discount-cactus/LVDC-Remake/LVDC-Parts-Kicad/3dmodels/LDL1117S50R.step

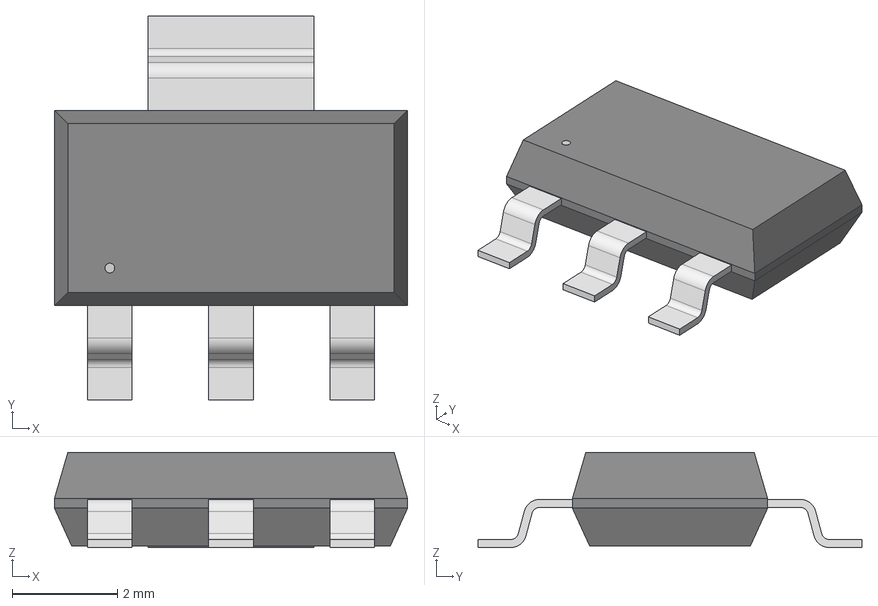
[picture p15: CAD file, 2024-02-13]
LVDC-Parts-Kicad/3dmodels/LDL1117S50R.step
6.71 x 7.29 x 1.81 mm
