discount-cactus/LVDC-Remake/LVDC-Parts-Kicad/3dmodels/TS50P07G.step

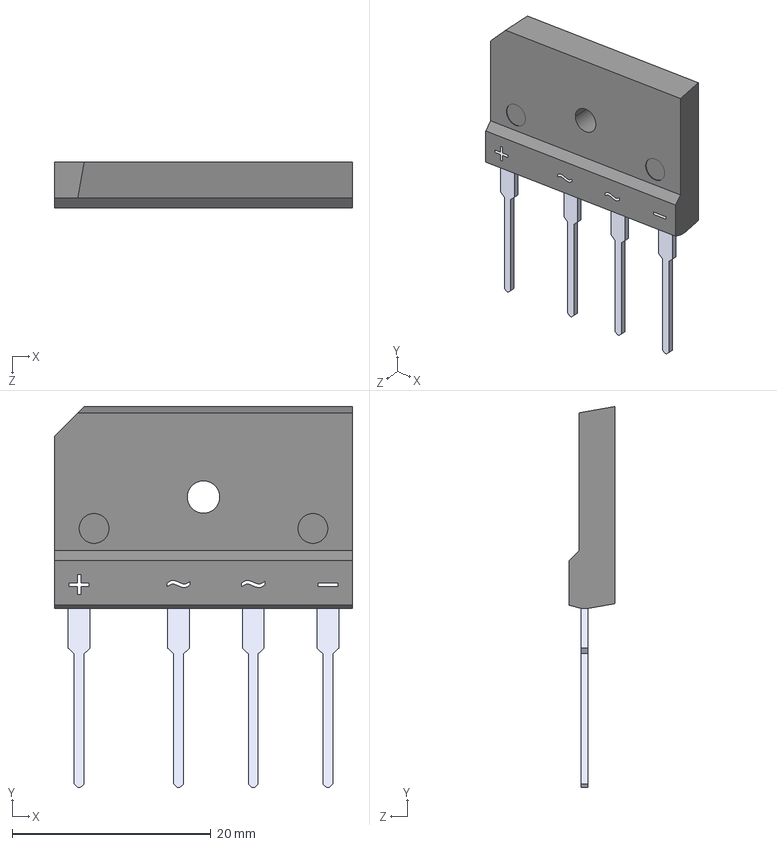
[picture p16: CAD file, 2024-02-13]
LVDC-Parts-Kicad/3dmodels/TS50P07G.step
30.0 x 38.3 x 4.60 mm
