discount-cactus/LVDC-Remake/LVDC-Parts-Kicad/3dmodels/DS3231M+TRL.step

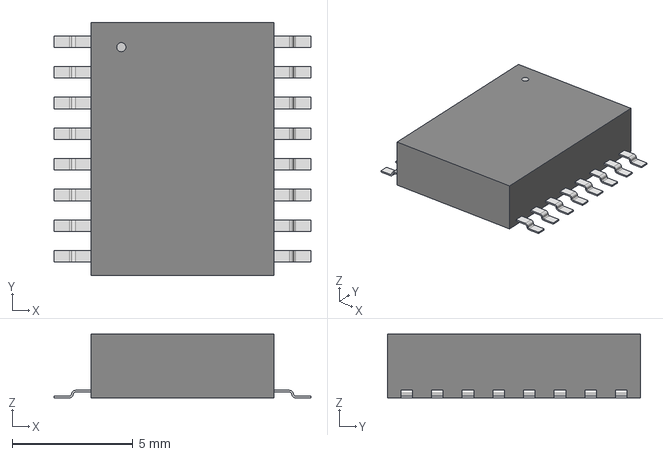
[picture p17: CAD file, 2024-02-13]
LVDC-Parts-Kicad/3dmodels/DS3231M+TRL.step
10.6 x 10.5 x 2.64 mm
