discount-cactus/LVDC-Remake/LVDC-Parts-Kicad/3dmodels/1043P.step

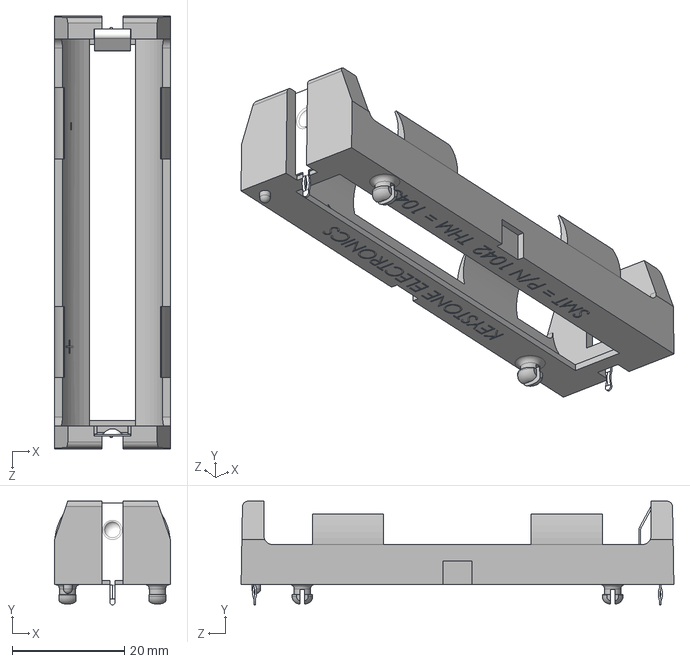
[picture p18: CAD file, 2024-02-13]
LVDC-Parts-Kicad/3dmodels/1043P.step
20.7 x 18.5 x 77.1 mm
