discount-cactus/LVDC-Remake/LVDC-Parts-Kicad/3dmodels/HEATSINK_658-45ABT4E.step

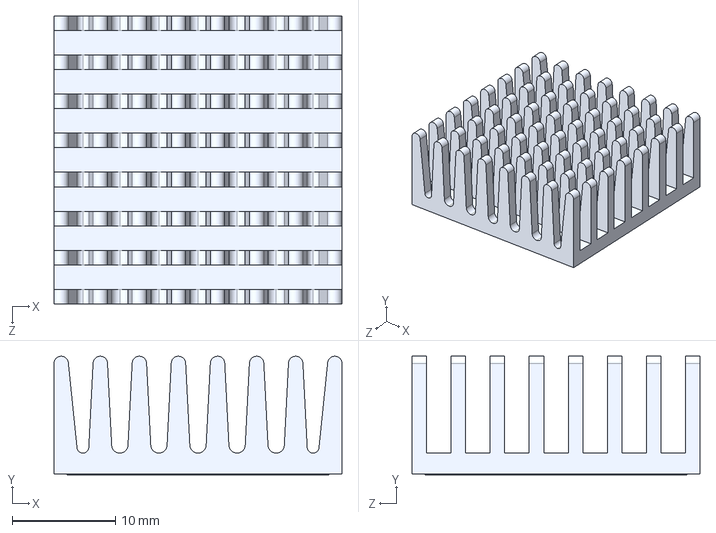
[picture p19: CAD file, 2024-02-13]
LVDC-Parts-Kicad/3dmodels/HEATSINK_658-45ABT4E.step
27.9 x 11.5 x 27.9 mm
