discount-cactus/LVDC-Remake/LVDC-Parts-Kicad/3dmodels/NYC0102BLT1G.step

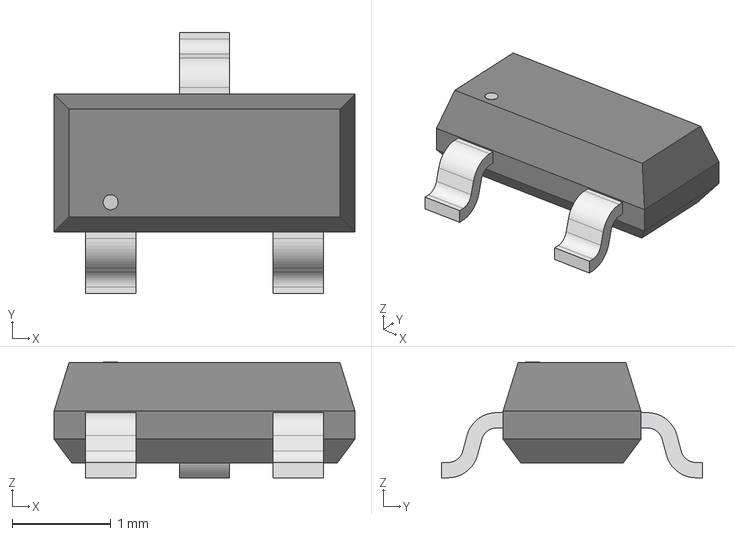
[picture p20: CAD file, 2024-02-13]
LVDC-Parts-Kicad/3dmodels/NYC0102BLT1G.step
3.05 x 2.64 x 1.17 mm
