discount-cactus/LVDC-Remake/LVDC-Parts-Kicad/3dmodels/6PCV_08_006.step

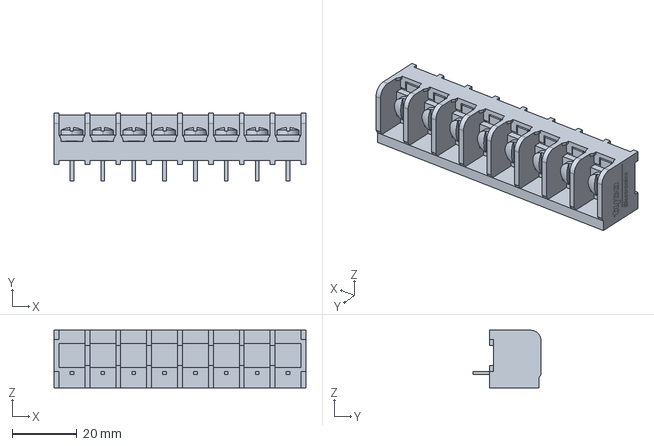
[picture p21: CAD file, 2024-02-13]
LVDC-Parts-Kicad/3dmodels/6PCV_08_006.step
77.7 x 21.0 x 17.8 mm
