discount-cactus/LVDC-Remake/LVDC-Parts-Kicad/3dmodels/TCLD1000.step

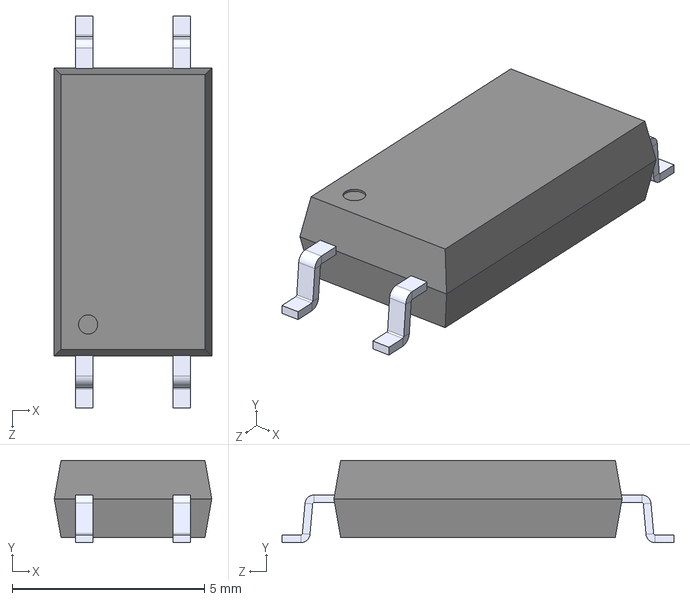
[picture p22: CAD file, 2024-02-13]
LVDC-Parts-Kicad/3dmodels/TCLD1000.step
4.10 x 2.14 x 10.2 mm
