discount-cactus/LVDC-Remake/LVDC-Parts-Kicad/3dmodels/PS2702-1-F3-A.step

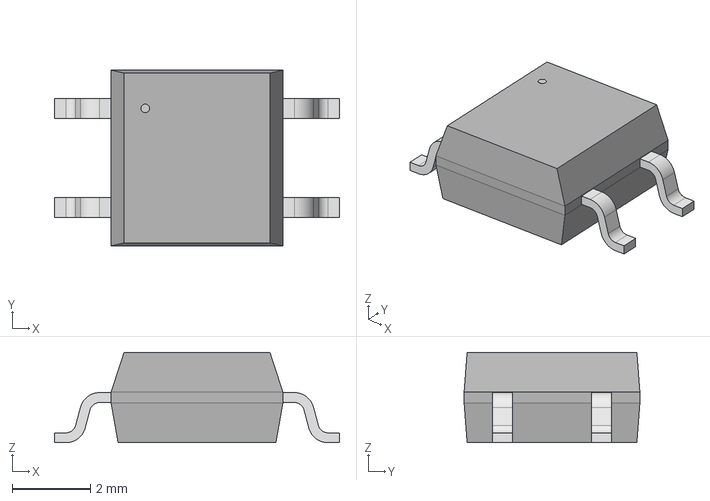
[picture p23: CAD file, 2024-02-13]
LVDC-Parts-Kicad/3dmodels/PS2702-1-F3-A.step
7.29 x 4.50 x 2.31 mm
