discount-cactus/LVDC-Remake/LVDC-Parts-Kicad/3dmodels/PDZVTR12B.step

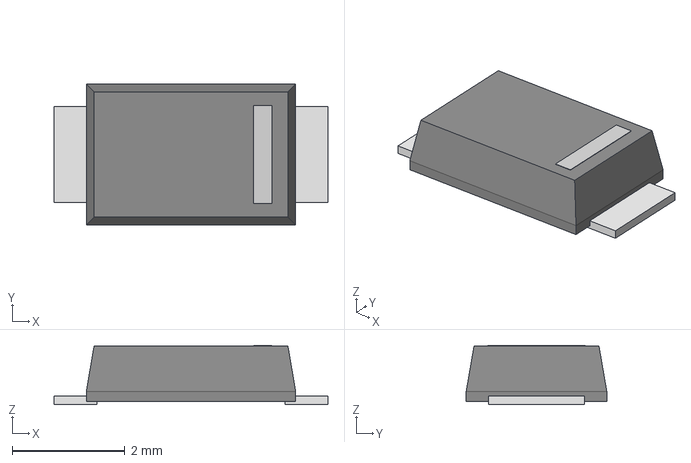
[picture p24: CAD file, 2024-02-13]
LVDC-Parts-Kicad/3dmodels/PDZVTR12B.step
4.85 x 2.49 x 1.05 mm
