discount-cactus/LVDC-Remake/LVDC-Parts-Kicad/3dmodels/SK510A_LTP.step

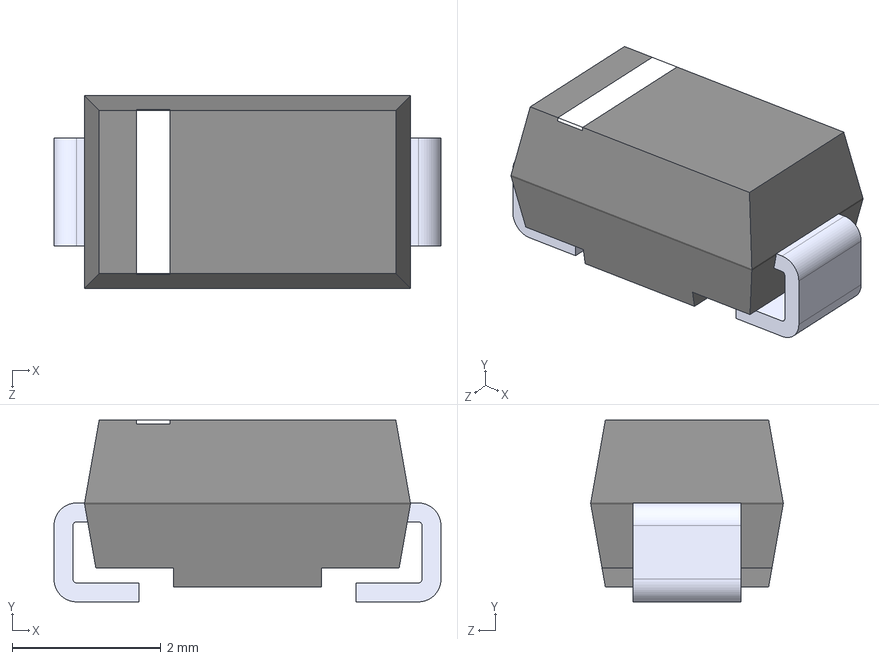
[picture p25: CAD file, 2024-02-13]
LVDC-Parts-Kicad/3dmodels/SK510A_LTP.step
5.20 x 2.44 x 2.58 mm
