discount-cactus/LVDC-Remake/LVDC-Parts-Kicad/3dmodels/MMSZ5240BT3G.step

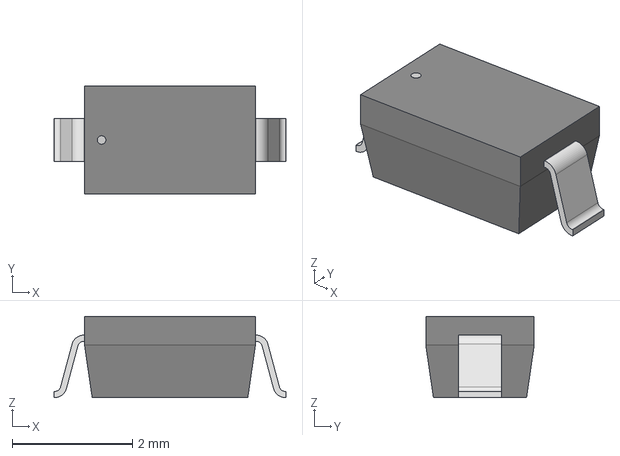
[picture p26: CAD file, 2024-02-13]
LVDC-Parts-Kicad/3dmodels/MMSZ5240BT3G.step
3.86 x 1.80 x 1.35 mm
