discount-cactus/LVDC-Remake/LVDC-Parts-Kicad/3dmodels/1101M2S3CQE2.step

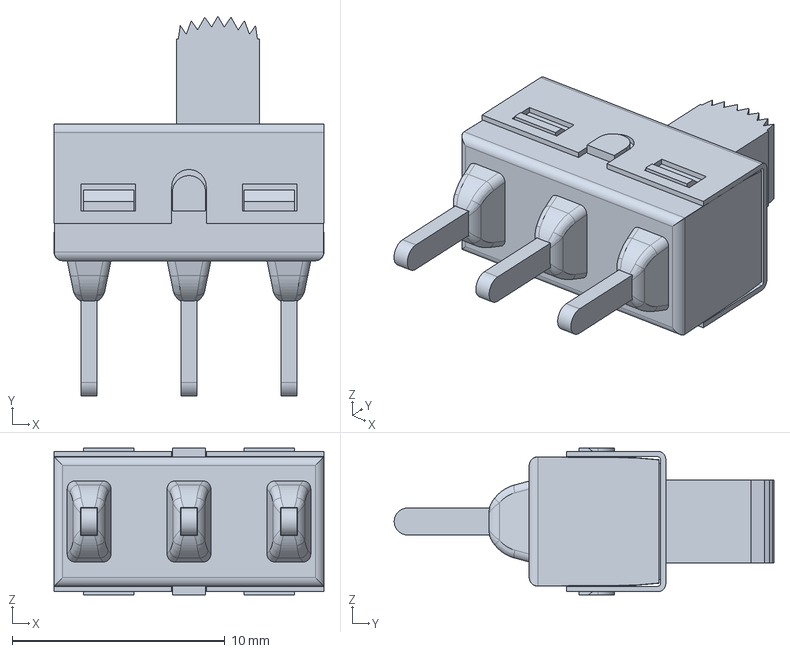
[picture p27: CAD file, 2024-02-13]
LVDC-Parts-Kicad/3dmodels/1101M2S3CQE2.step
12.7 x 17.9 x 6.91 mm
