discount-cactus/LVDC-Remake/LVDC-Parts-Kicad/3dmodels/HEATSINK_v2016b.step

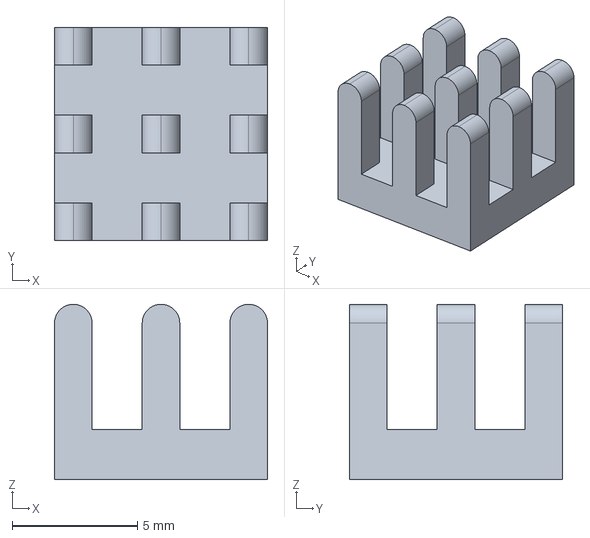
[picture p28: CAD file, 2024-02-13]
LVDC-Parts-Kicad/3dmodels/HEATSINK_v2016b.step
8.50 x 8.50 x 7.00 mm
