discount-cactus/LVDC-Remake/LVDC-Parts-Kicad/3dmodels/fan_30mm.step

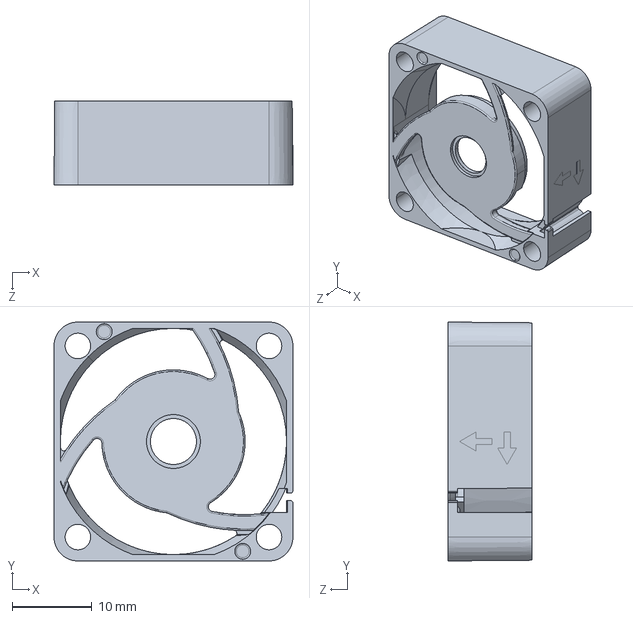
[picture p29: CAD file, 2024-02-13]
LVDC-Parts-Kicad/3dmodels/fan_30mm.step
30.0 x 30.0 x 10.5 mm
