discount-cactus/LVDC-Remake/LVDC-Parts-Kicad/3dmodels/1x6.step

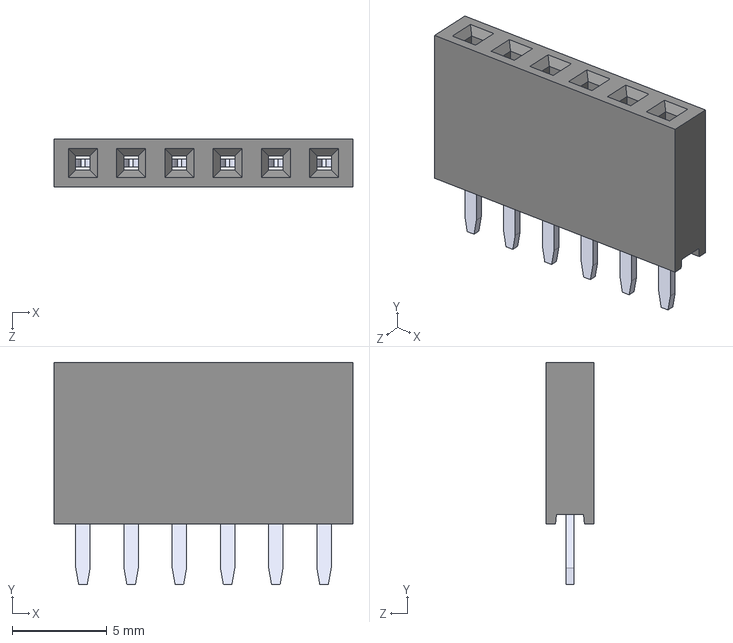
[picture p30: CAD file, 2024-02-13]
LVDC-Parts-Kicad/3dmodels/1x6.step
15.7 x 11.7 x 2.54 mm
