discount-cactus/LVDC-Remake/LVDC-Parts-Kicad/3dmodels/G5PZ-1A-E-DC5.step

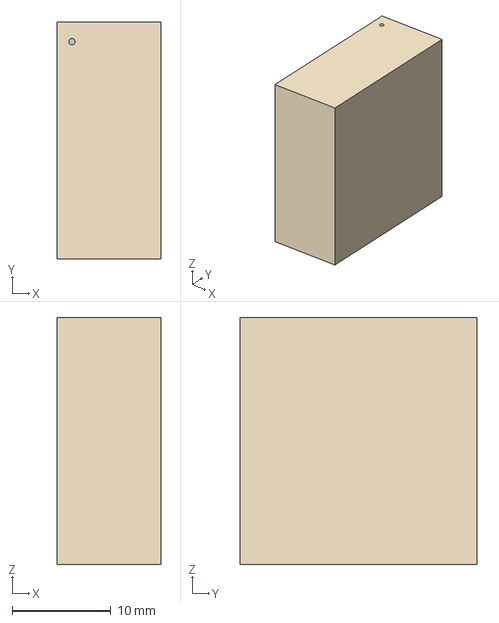
[picture p31: CAD file, 2024-02-13]
LVDC-Parts-Kicad/3dmodels/G5PZ-1A-E-DC5.step
10.5 x 24.0 x 25.0 mm
