discount-cactus/LVDC-Remake/LVDC-Parts-Kicad/3dmodels/SIC431AED-T1-GE3.step

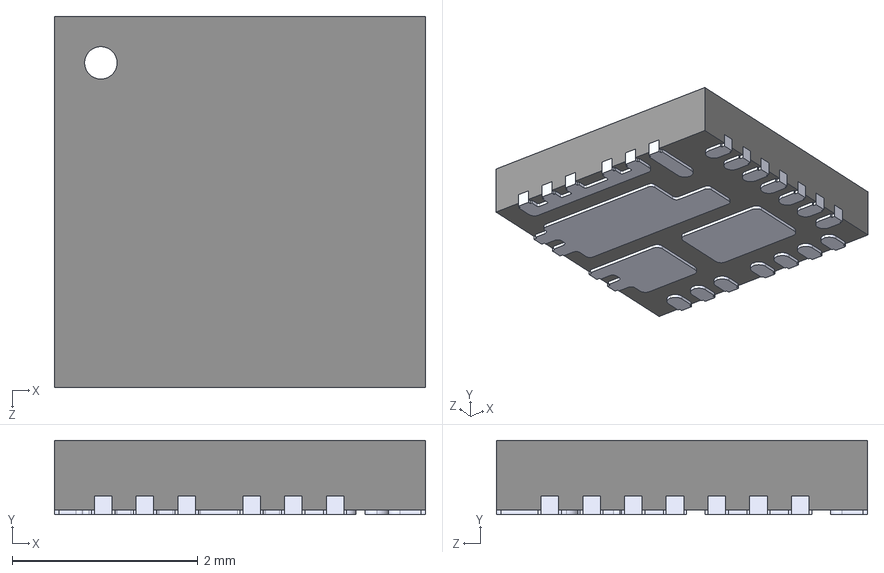
[picture p32: CAD file, 2024-02-13]
LVDC-Parts-Kicad/3dmodels/SIC431AED-T1-GE3.step
4.00 x 0.8 x 4.00 mm
