discount-cactus/LVDC-Remake/LVDC-Parts-Kicad/3dmodels/SBR10U200P5-13.step

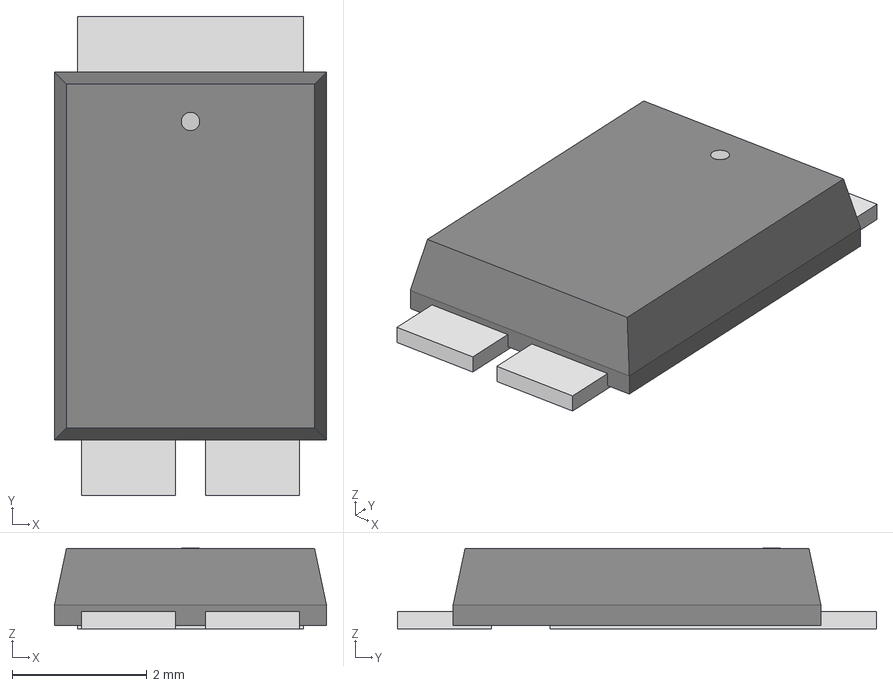
[picture p33: CAD file, 2024-02-13]
LVDC-Parts-Kicad/3dmodels/SBR10U200P5-13.step
4.04 x 7.11 x 1.20 mm
