discount-cactus/LVDC-Remake/LVDC-Parts-Kicad/3dmodels/MEM2051-00-195-00-A.step

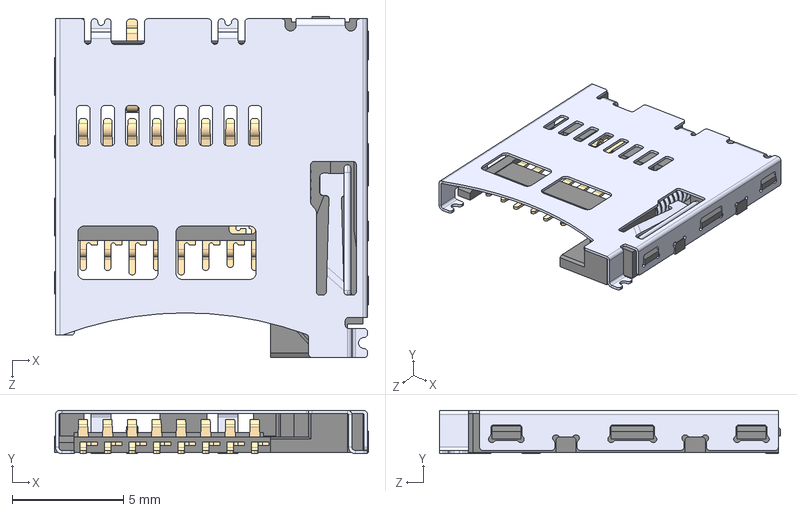
[picture p34: CAD file, 2024-02-13]
LVDC-Parts-Kicad/3dmodels/MEM2051-00-195-00-A.step
14.1 x 1.95 x 15.3 mm
