discount-cactus/LVDC-Remake/LVDC-Parts-Kicad/3dmodels/8PCV_02_006.step

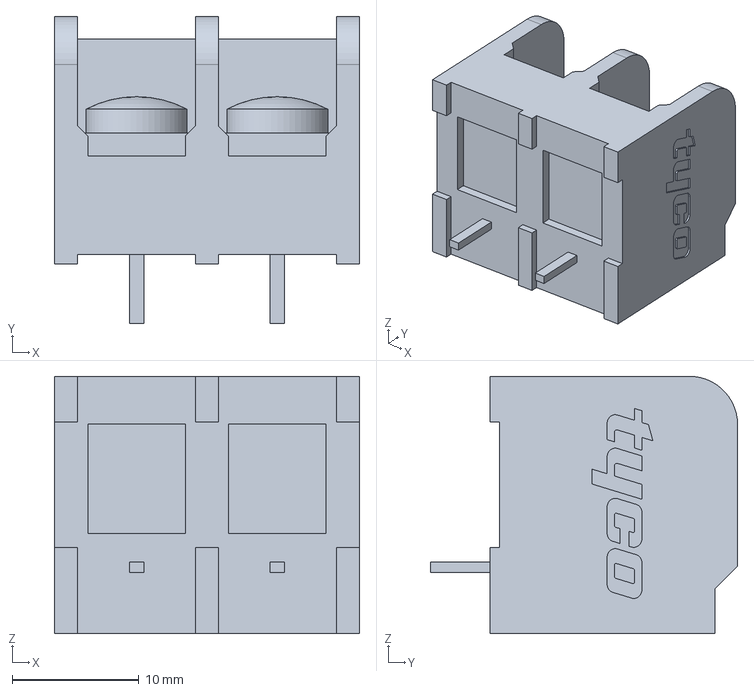
[picture p35: CAD file, 2024-02-13]
LVDC-Parts-Kicad/3dmodels/8PCV_02_006.step
24.1 x 24.3 x 20.3 mm
