discount-cactus/LVDC-Remake/LVDC-Parts-Kicad/3dmodels/G2RL_1A_E2_CV_HA.step

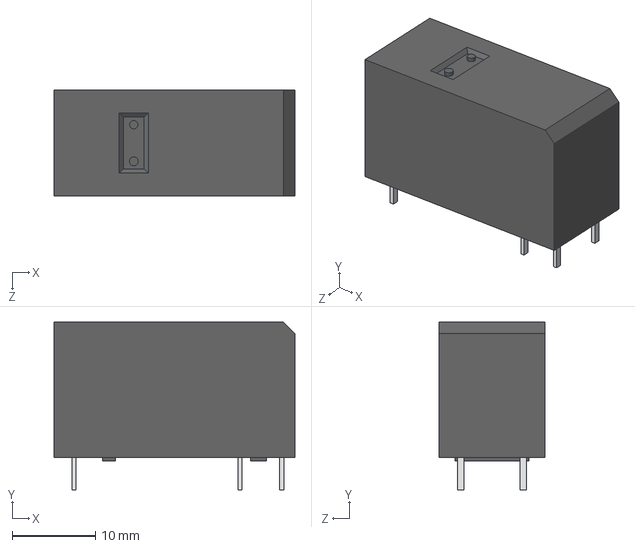
[picture p36: CAD file, 2024-02-13]
LVDC-Parts-Kicad/3dmodels/G2RL_1A_E2_CV_HA.step
29.0 x 20.2 x 12.7 mm
