discount-cactus/LVDC-Remake/LVDC-Parts-Kicad/3dmodels/Fuse_15A.step

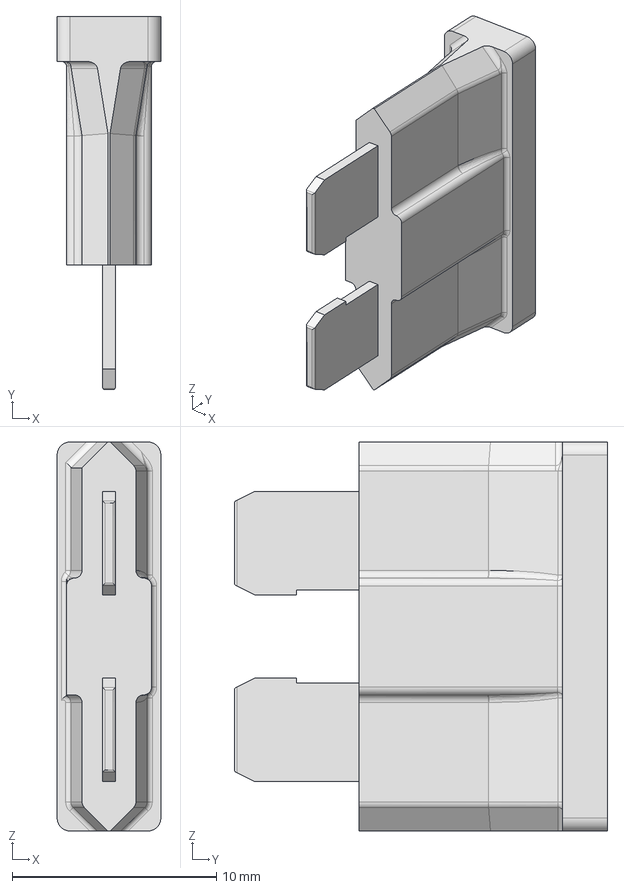
[picture p37: CAD file, 2023-09-17]
LVDC-Parts-Kicad/3dmodels/Fuse_15A.step
5.08 x 18.3 x 19.0 mm
