discount-cactus/LVDC-Remake/LVDC-Parts-Kicad/3dmodels/1x14.step

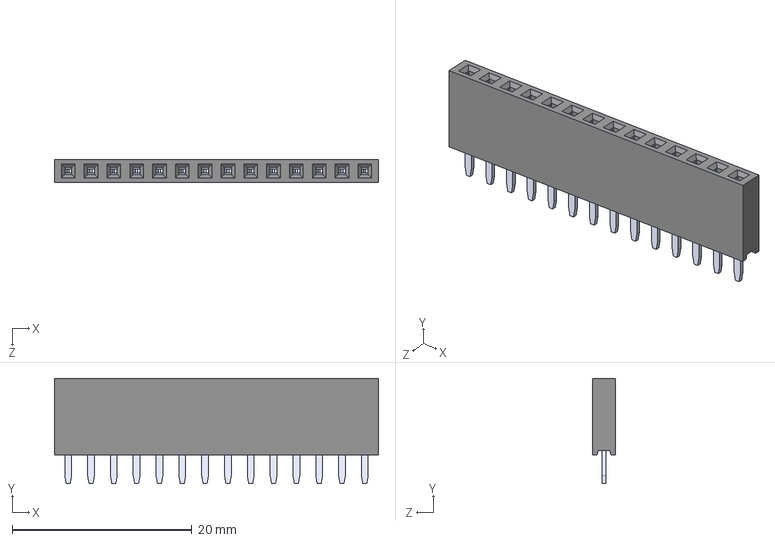
[picture p38: CAD file, 2023-08-25]
LVDC-Parts-Kicad/3dmodels/1x14.step
36.1 x 11.7 x 2.54 mm
