discount-cactus/LVDC-Remake/LVDC-Parts-Kicad/3dmodels/L7805CV.step

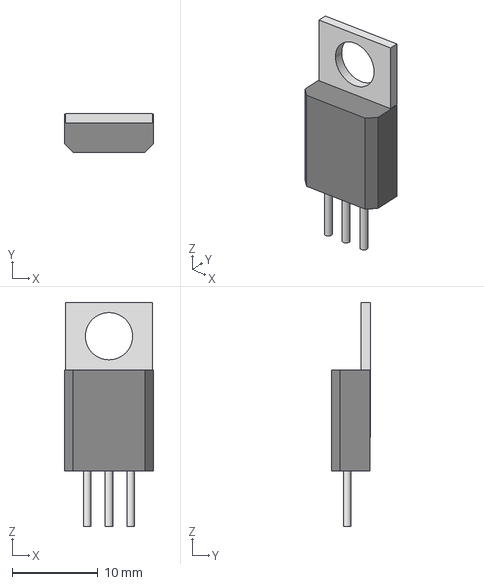
[picture p39: CAD file, 2023-08-25]
LVDC-Parts-Kicad/3dmodels/L7805CV.step
10.4 x 4.60 x 26.2 mm
