discount-cactus/LVDC-Remake/LVDC-Parts-Kicad/3dmodels/SN74HCS30PWR.STEP

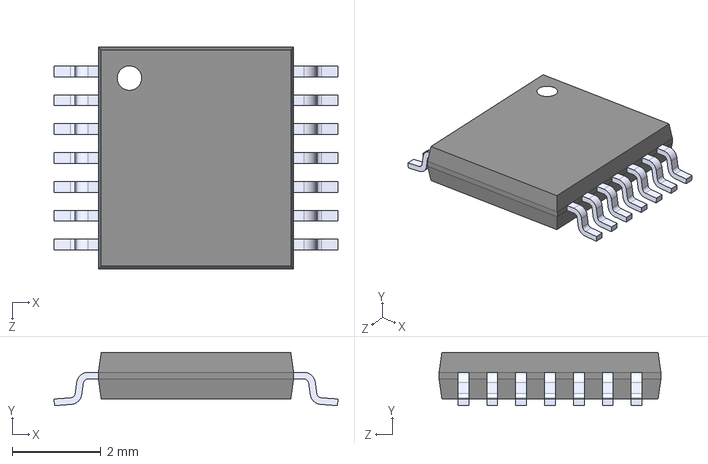
[picture p40: CAD file, 2023-08-25]
LVDC-Parts-Kicad/3dmodels/SN74HCS30PWR.STEP
6.40 x 1.20 x 5.00 mm
