discount-cactus/LVDC-Remake/LVDC-Parts-Kicad/3dmodels/1x10.step

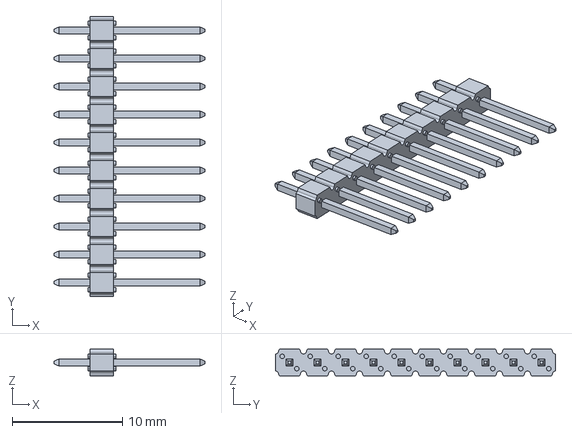
[picture p41: CAD file, 2023-08-25]
LVDC-Parts-Kicad/3dmodels/1x10.step
13.7 x 25.4 x 2.41 mm
