discount-cactus/LVDC-Remake/LVDC-Parts-Kicad/3dmodels/A767KN476M1HLAE029.step

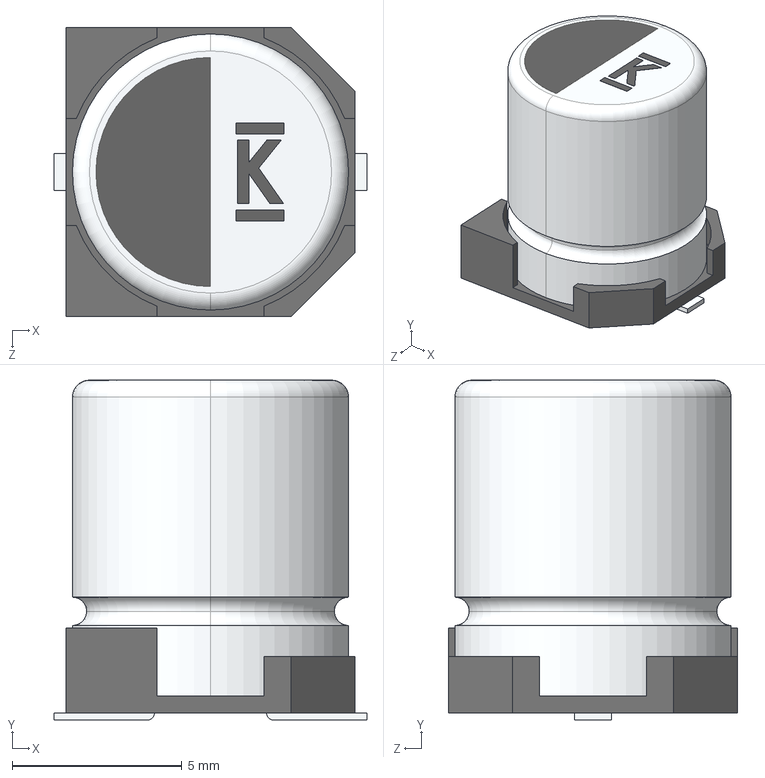
[picture p42: CAD file, 2023-08-25]
LVDC-Parts-Kicad/3dmodels/A767KN476M1HLAE029.step
9.20 x 10.0 x 8.50 mm
