discount-cactus/LVDC-Remake/LVDC-Parts-Kicad/3dmodels/2x19.step

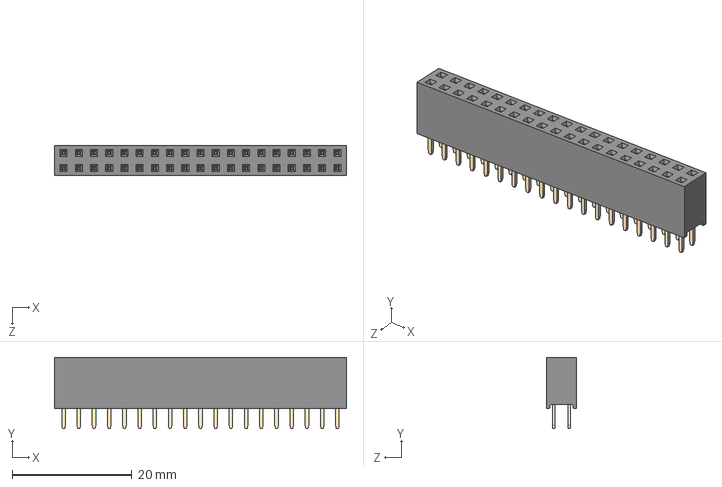
[picture p43: CAD file, 2023-08-25]
LVDC-Parts-Kicad/3dmodels/2x19.step
48.8 x 11.9 x 5.08 mm
2 row tin body_19
2 row tin pins x 19
