discount-cactus/LVDC-Remake/LVDC-Parts-Kicad/3dmodels/2x13.step

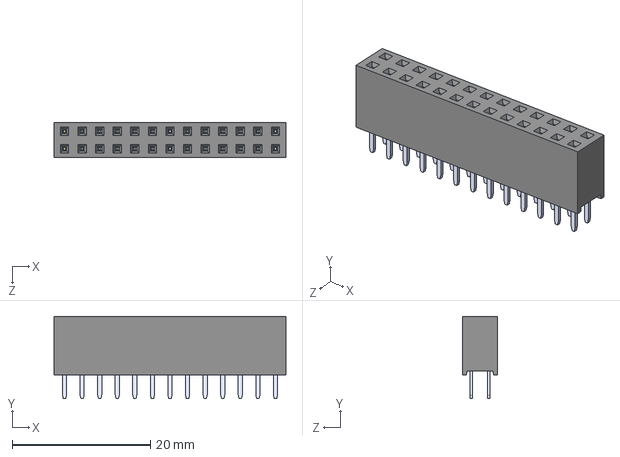
[picture p44: CAD file, 2023-08-25]
LVDC-Parts-Kicad/3dmodels/2x13.step
33.5 x 11.9 x 5.08 mm
2 row tin body_13
2 row tin pins x 13
