discount-cactus/LVDC-Remake/LVDC-Parts-Kicad/3dmodels/LM350T.step

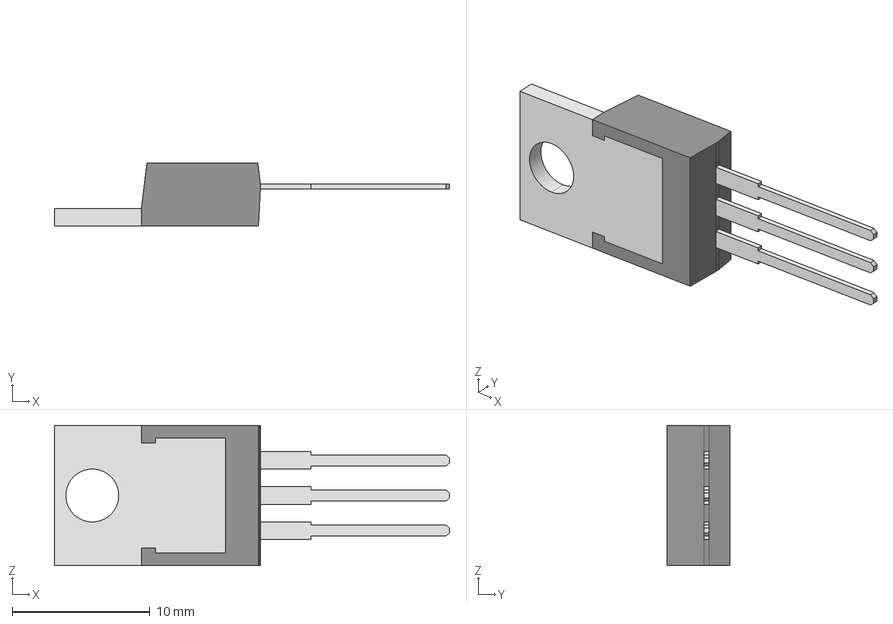
[picture p45: CAD file, 2023-08-25]
LVDC-Parts-Kicad/3dmodels/LM350T.step
28.7 x 4.57 x 10.2 mm
T03B_BODY
T03B_LEAD x 3
T03B_HS
