discount-cactus/LVDC-Remake/LVDC-Parts-Kicad/3dmodels/1N4736A.step

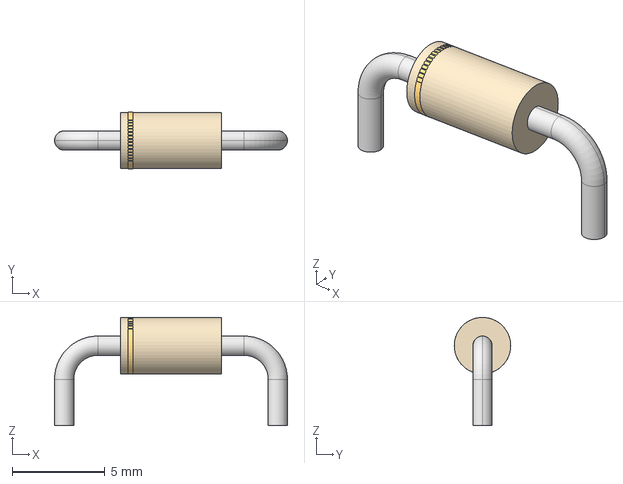
[picture p46: CAD file, 2023-08-25]
LVDC-Parts-Kicad/3dmodels/1N4736A.step
12.6 x 3.05 x 5.84 mm
