discount-cactus/LVDC-Remake/LVDC-Parts-Kicad/3dmodels/SRR1208-6R5ML.step

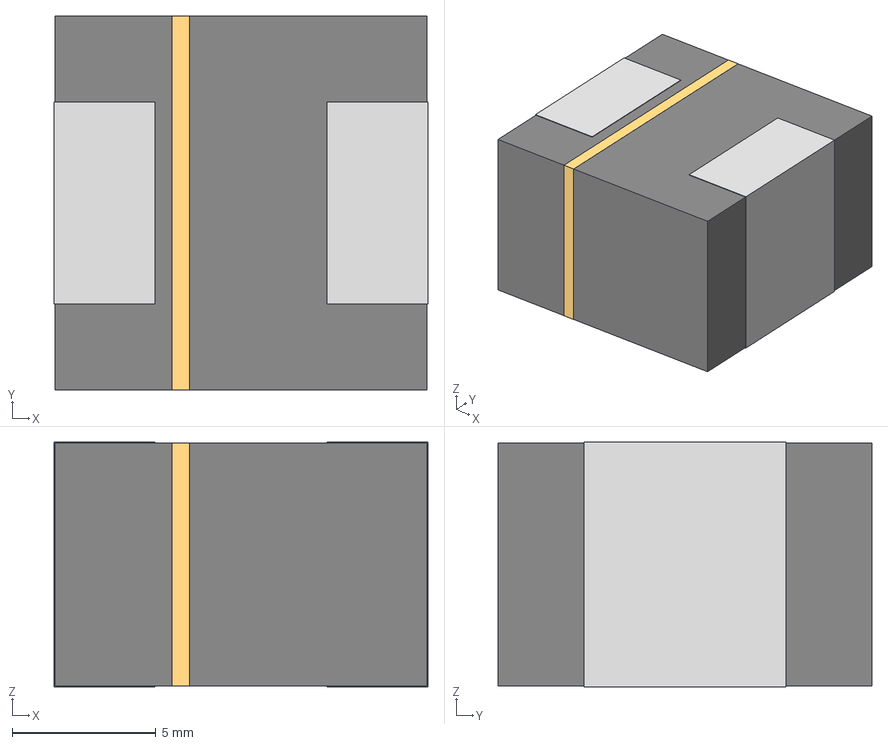
[picture p47: CAD file, 2023-08-25]
LVDC-Parts-Kicad/3dmodels/SRR1208-6R5ML.step
13.0 x 13.0 x 8.51 mm
