discount-cactus/LVDC-Remake/LVDC-Parts-Kicad/3dmodels/C_PTH_680uF.step

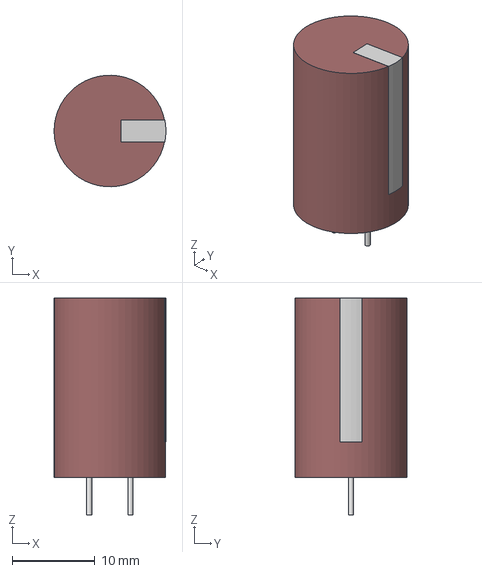
[picture p48: CAD file, 2023-08-25]
LVDC-Parts-Kicad/3dmodels/C_PTH_680uF.step
13.5 x 13.5 x 26.3 mm
