discount-cactus/LVDC-Remake/LVDC-Parts-Kicad/3dmodels/2x18.step

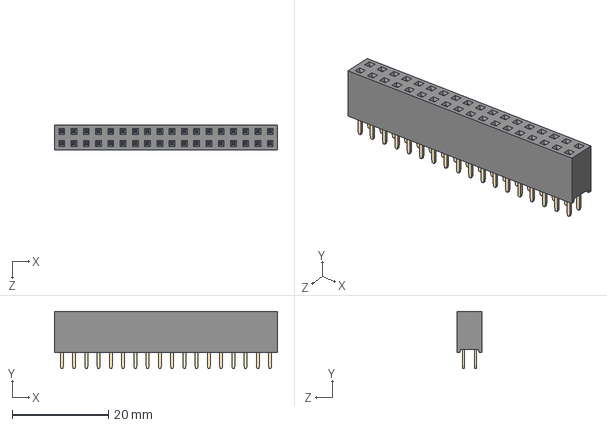
[picture p49: CAD file, 2023-08-25]
LVDC-Parts-Kicad/3dmodels/2x18.step
46.2 x 11.9 x 5.08 mm
2 row tin body_18
2 row tin pins x 18
