discount-cactus/LVDC-Remake/LVDC-Parts-Kicad/3dmodels/AMC1301QDWVQ1.step

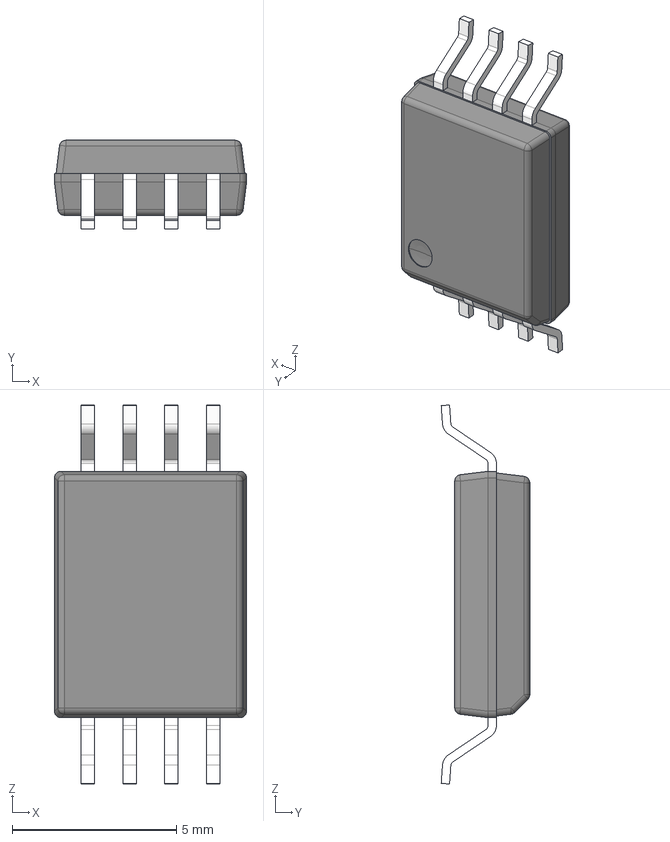
[picture p50: CAD file, 2023-08-25]
LVDC-Parts-Kicad/3dmodels/AMC1301QDWVQ1.step
5.85 x 2.70 x 11.5 mm
BODY-SOIC
LEAD-DWV0008A x 8
