discount-cactus/LVDC-Remake/LVDC-Parts-Kicad/3dmodels/2x12.step

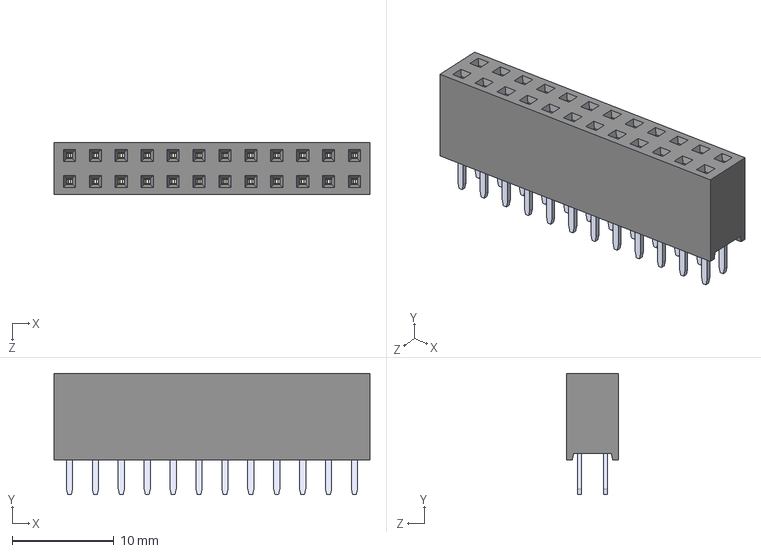
[picture p51: CAD file, 2023-08-25]
LVDC-Parts-Kicad/3dmodels/2x12.step
31.0 x 11.9 x 5.08 mm
2 row tin body_12
2 row tin pins x 12
