discount-cactus/LVDC-Remake/LVDC-Parts-Kicad/3dmodels/SOD_128.step

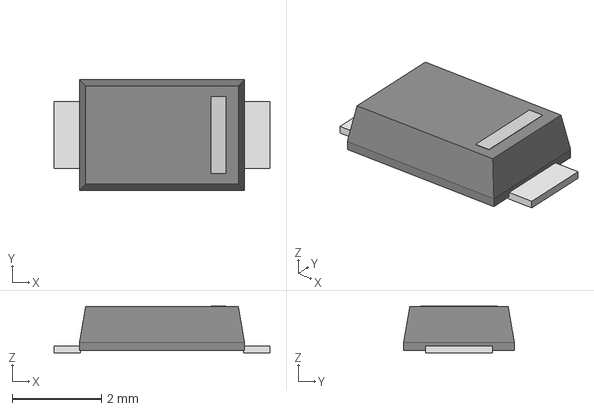
[picture p52: CAD file, 2023-08-25]
LVDC-Parts-Kicad/3dmodels/SOD_128.step
4.85 x 2.49 x 1.05 mm
