discount-cactus/LVDC-Remake/LVDC-Parts-Kicad/3dmodels/2x2.step

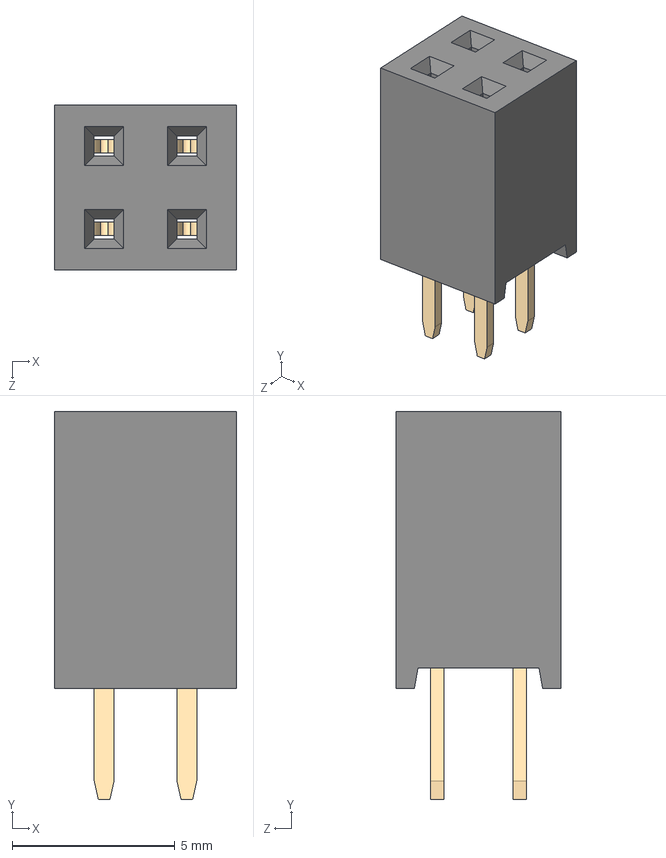
[picture p53: CAD file, 2023-08-25]
LVDC-Parts-Kicad/3dmodels/2x2.step
5.59 x 11.9 x 5.08 mm
2 row tin body_02
2 row tin pins x 2
