discount-cactus/LVDC-Remake/LVDC-Parts-Kicad/3dmodels/INA210AIDCKR.step

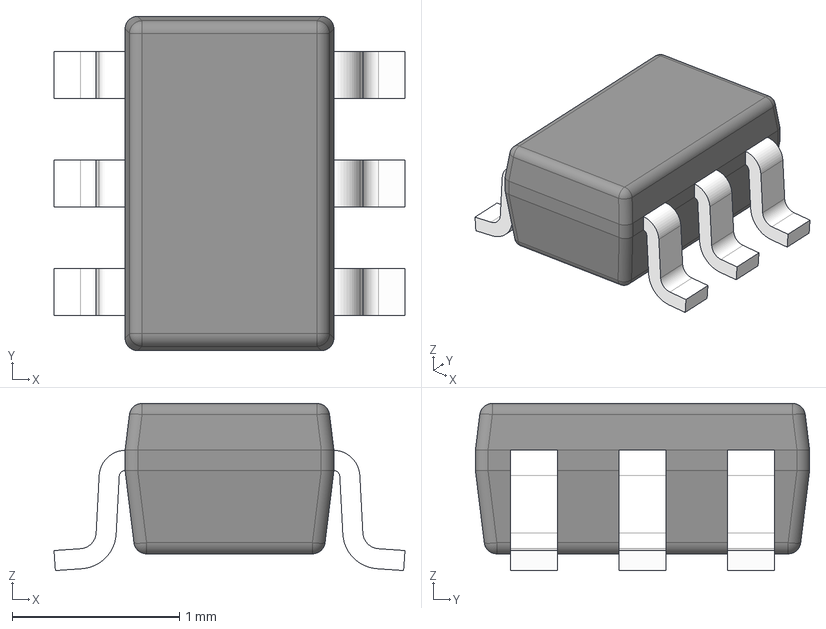
[picture p54: CAD file, 2023-08-25]
LVDC-Parts-Kicad/3dmodels/INA210AIDCKR.step
2.10 x 2.00 x 1.00 mm
BODY-SOT
LEAD-SOT x 6
PIN1-ID
