discount-cactus/LVDC-Remake/LVDC-Parts-Kicad/3dmodels/A750MV477M1VAAE018.step

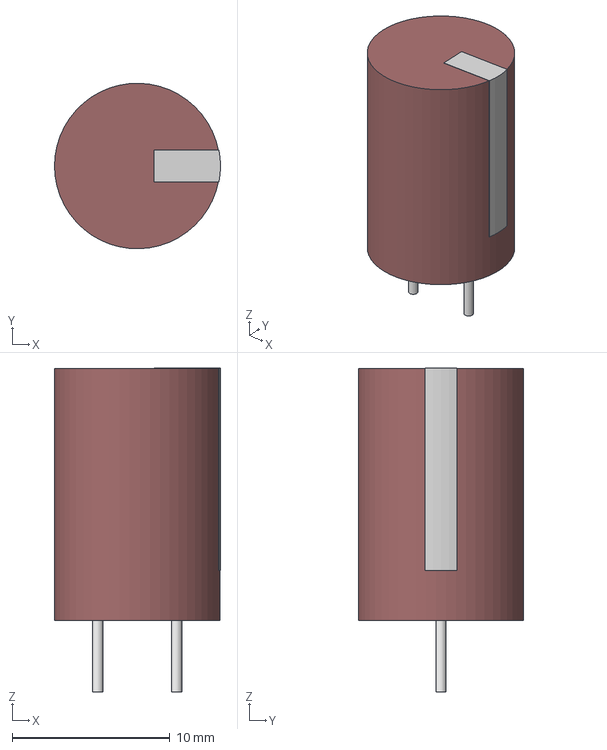
[picture p55: CAD file, 2023-08-25]
LVDC-Parts-Kicad/3dmodels/A750MV477M1VAAE018.step
10.5 x 10.5 x 20.5 mm
