discount-cactus/LVDC-Remake/LVDC-Parts-Kicad/3dmodels/DO-214BA.step

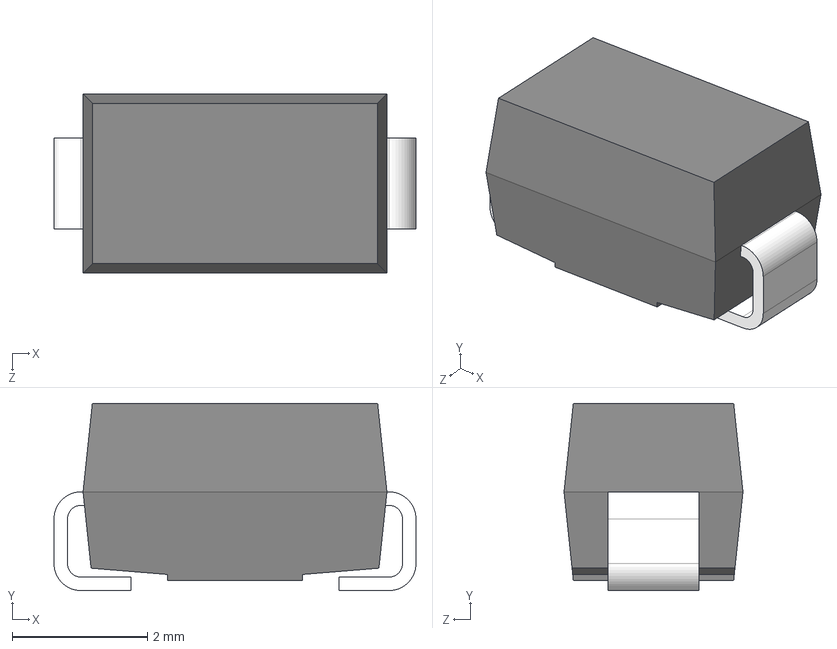
[picture p56: CAD file, 2023-08-25]
LVDC-Parts-Kicad/3dmodels/DO-214BA.step
5.36 x 2.77 x 2.65 mm
