discount-cactus/LVDC-Remake/LVDC-Parts-Kicad/3dmodels/2x23.step

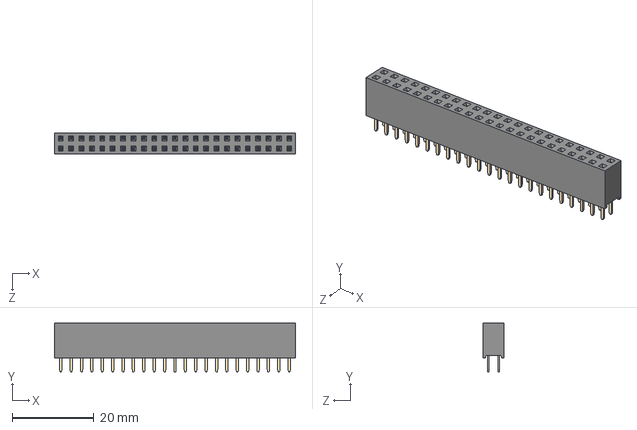
[picture p57: CAD file, 2023-08-25]
LVDC-Parts-Kicad/3dmodels/2x23.step
58.9 x 11.9 x 5.08 mm
2 row tin body_23
2 row tin pins x 23
