discount-cactus/LVDC-Remake/LVDC-Parts-Kicad/3dmodels/ETQ-P6F4R1LFA.step

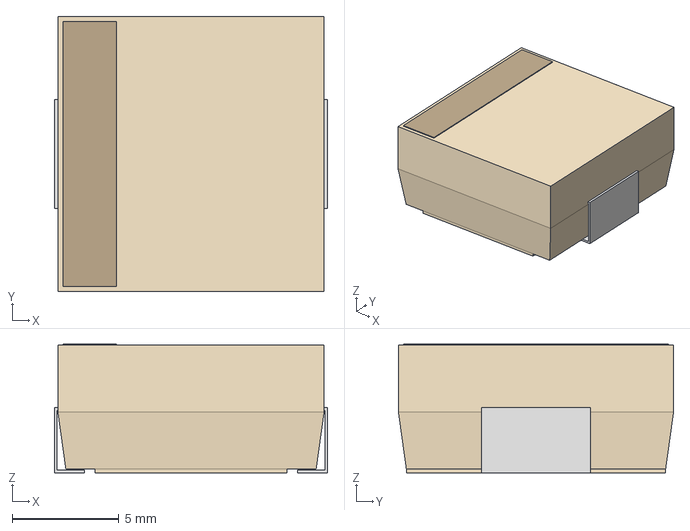
[picture p58: CAD file, 2023-08-25]
LVDC-Parts-Kicad/3dmodels/ETQ-P6F4R1LFA.step
12.8 x 12.9 x 6.04 mm
