discount-cactus/LVDC-Remake/LVDC-Parts-Kicad/3dmodels/CAP_PTH.step

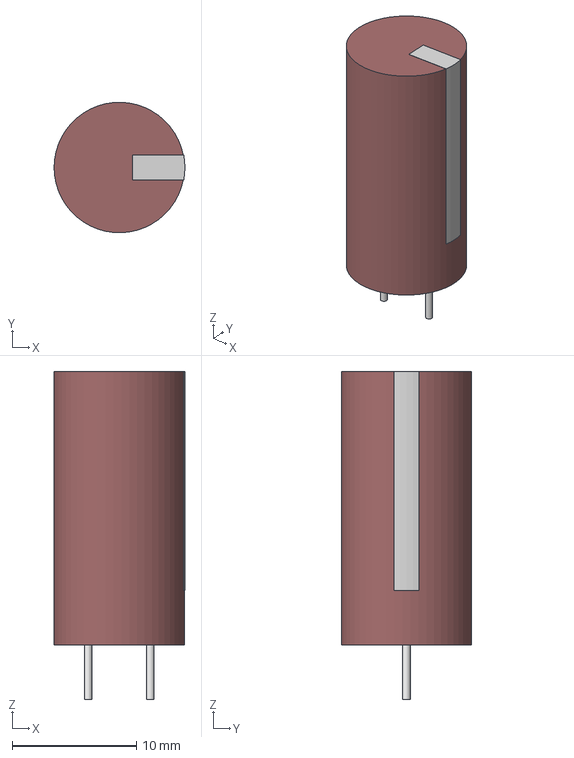
[picture p59: CAD file, 2023-05-30]
LVDC-Parts-Kicad/3dmodels/CAP_PTH.step
10.5 x 10.5 x 26.4 mm
