discount-cactus/LVDC-Remake/LVDC-Parts-Kicad/3dmodels/W5500.step

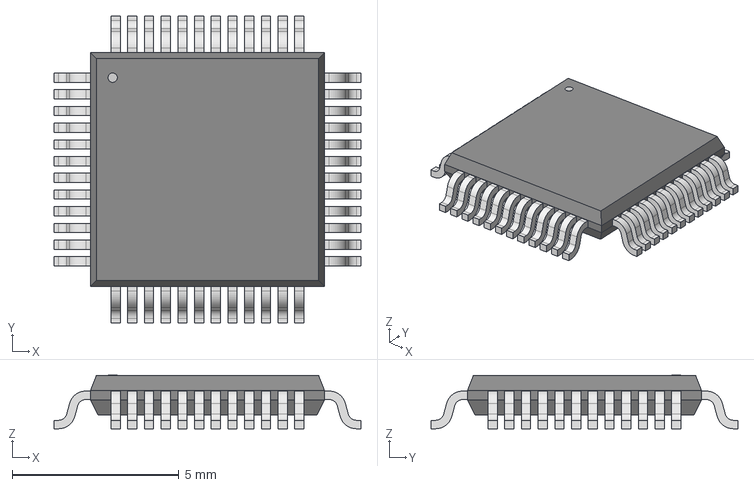
[picture p60: CAD file, 2023-05-30]
LVDC-Parts-Kicad/3dmodels/W5500.step
9.19 x 9.19 x 1.60 mm
