discount-cactus/LVDC-Remake/LVDC-Parts-Kicad/3dmodels/2x30.STEP

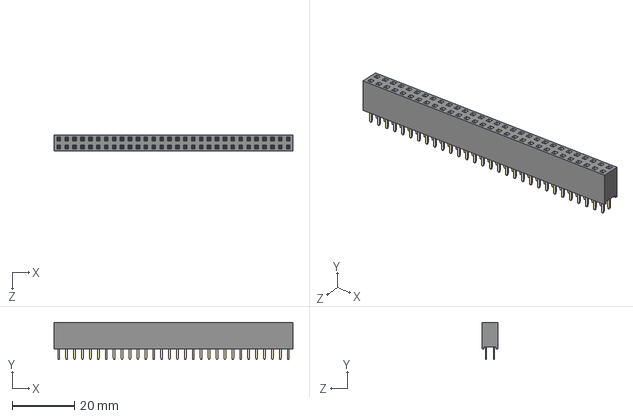
[picture p61: CAD file, 2023-05-30]
LVDC-Parts-Kicad/3dmodels/2x30.STEP
76.7 x 11.9 x 5.08 mm
2 row tin body_30
2 row tin pins x 30
