discount-cactus/LVDC-Remake/LVDC-Parts-Kicad/3dmodels/PPTC102LJBN-RC.step

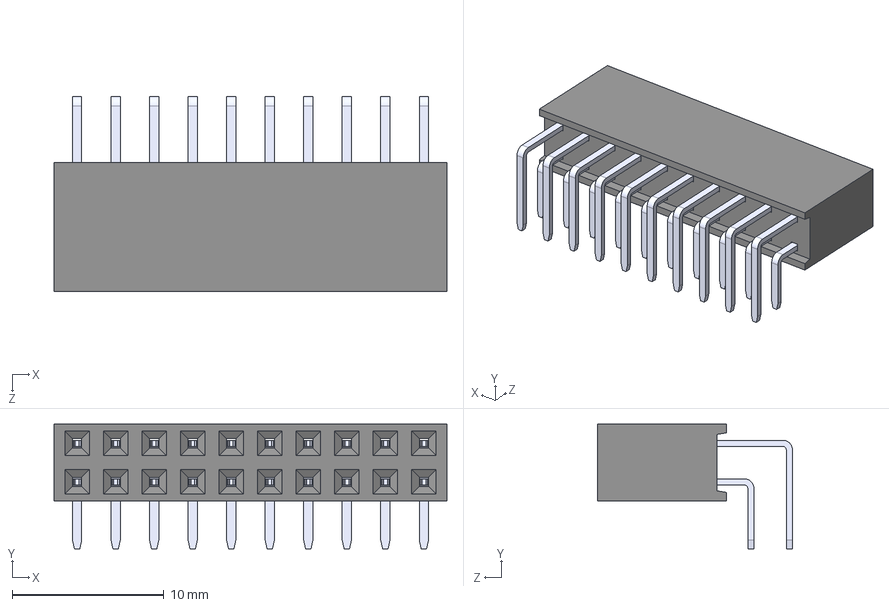
[picture p62: CAD file, 2023-05-30]
LVDC-Parts-Kicad/3dmodels/PPTC102LJBN-RC.step
25.9 x 8.23 x 12.9 mm
