discount-cactus/LVDC-Remake/LVDC-Parts-Kicad/3dmodels/FB_0805.step

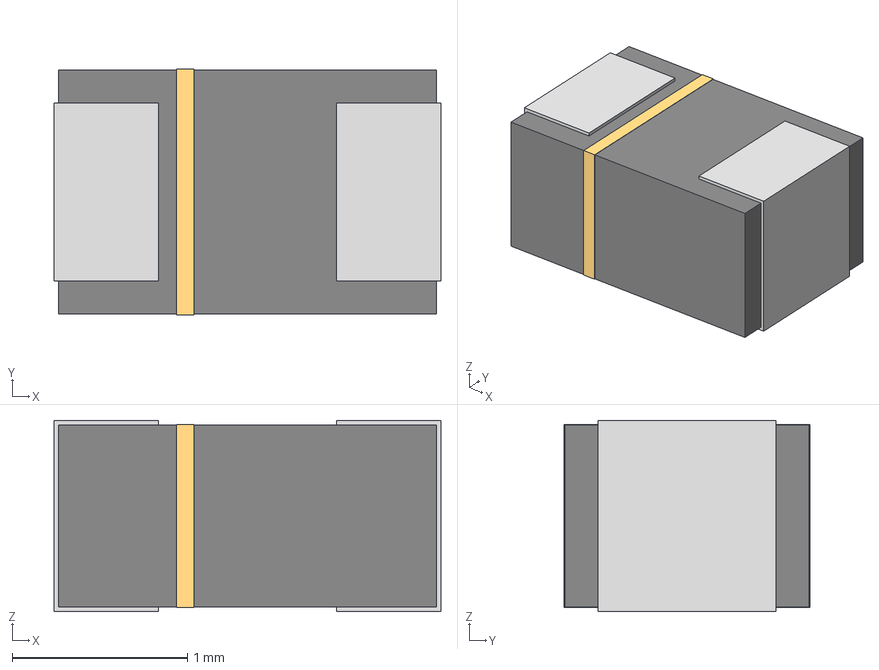
[picture p63: CAD file, 2023-05-30]
LVDC-Parts-Kicad/3dmodels/FB_0805.step
2.21 x 1.40 x 1.09 mm
