discount-cactus/LVDC-Remake/LVDC-Parts-Kicad/3dmodels/1x3.step

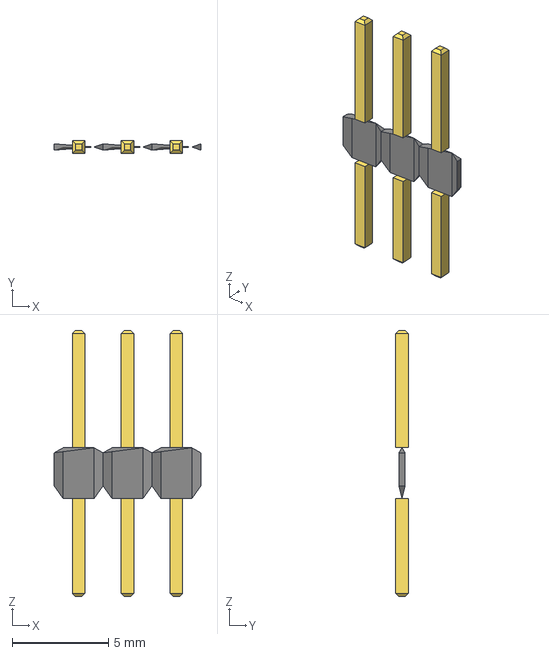
[picture p64: CAD file, 2023-05-30]
LVDC-Parts-Kicad/3dmodels/1x3.step
7.62 x 0.66 x 13.8 mm
