discount-cactus/LVDC-Remake/LVDC-Parts-Kicad/3dmodels/CD4002BNSR.step

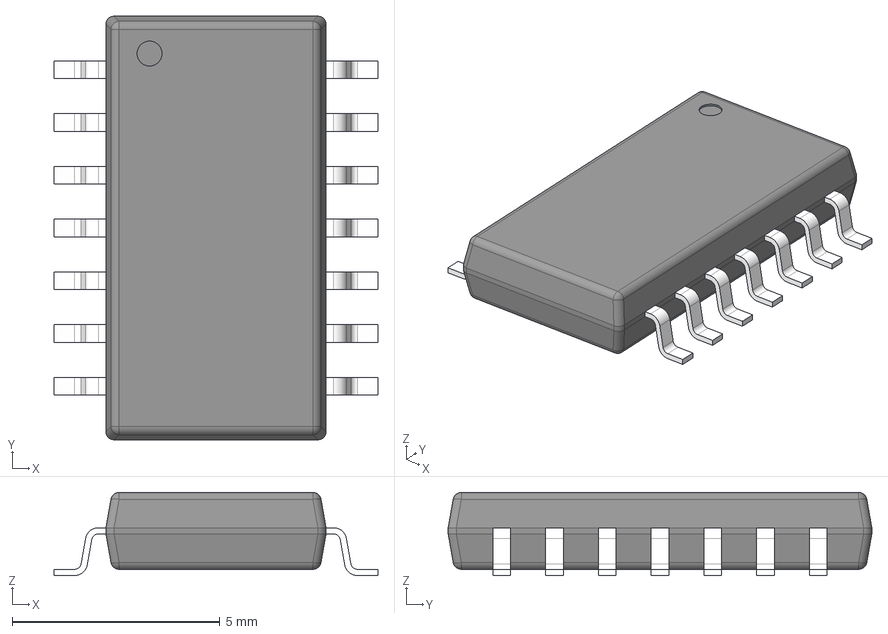
[picture p65: CAD file, 2023-05-30]
LVDC-Parts-Kicad/3dmodels/CD4002BNSR.step
7.80 x 10.2 x 2.00 mm
BODY-SO
LEAD-SO x 14
