discount-cactus/LVDC-Remake/LVDC-Parts-Kicad/3dmodels/2x5.step

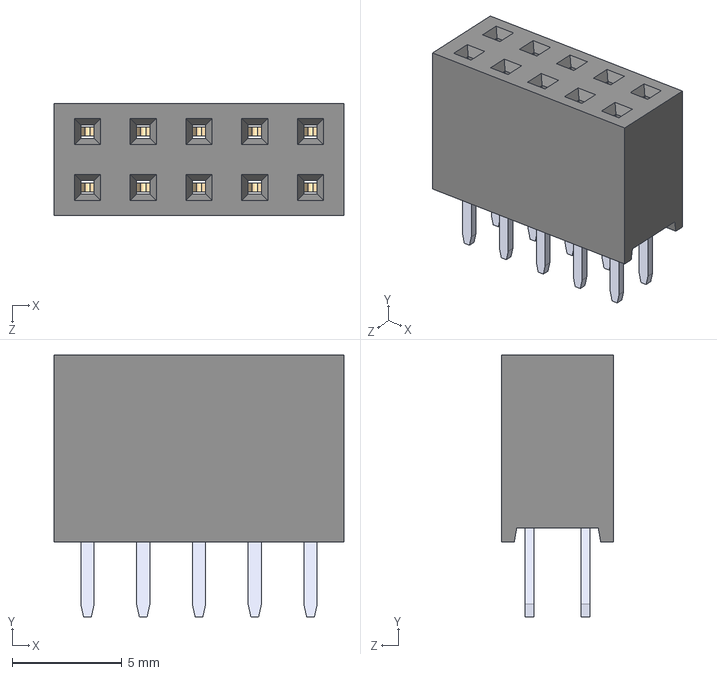
[picture p66: CAD file, 2023-05-30]
LVDC-Parts-Kicad/3dmodels/2x5.step
13.2 x 11.9 x 5.08 mm
2 row tin body_05
2 row tin pins x 5
