discount-cactus/LVDC-Remake/LVDC-Parts-Kicad/3dmodels/2x25.STEP

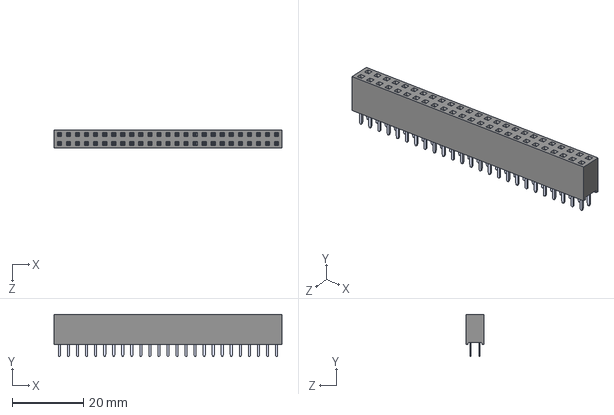
[picture p67: CAD file, 2023-05-30]
LVDC-Parts-Kicad/3dmodels/2x25.STEP
64.0 x 11.9 x 5.08 mm
2 row tin body_25
2 row tin pins x 25
