discount-cactus/LVDC-Remake/LVDC-Parts-Kicad/3dmodels/CD4012BM96.step

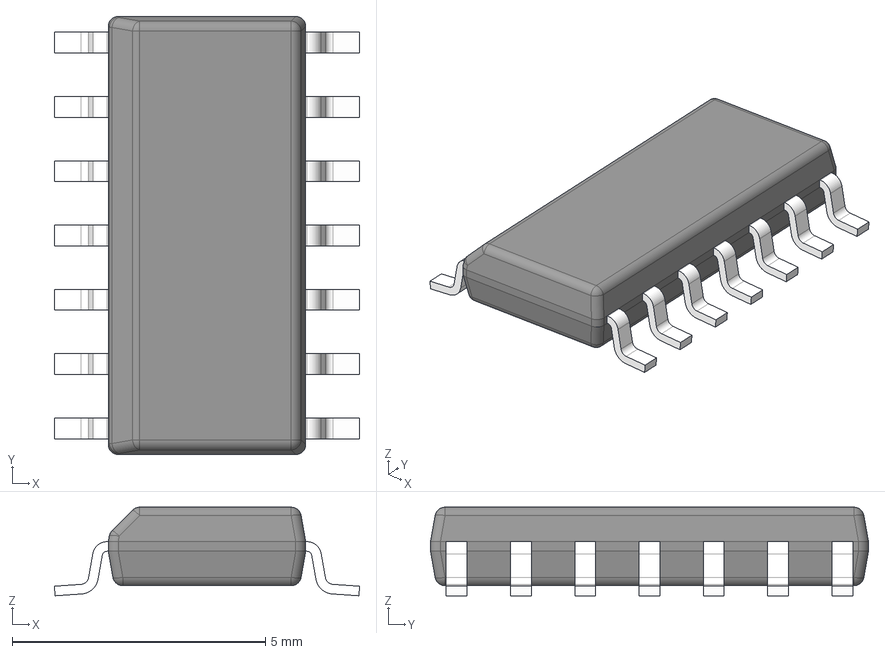
[picture p68: CAD file, 2023-05-30]
LVDC-Parts-Kicad/3dmodels/CD4012BM96.step
6.03 x 8.65 x 1.75 mm
BODY-SO
LEAD-SO x 14
PIN1-ID
