discount-cactus/LVDC-Remake/LVDC-Parts-Kicad/3dmodels/1x13.igs

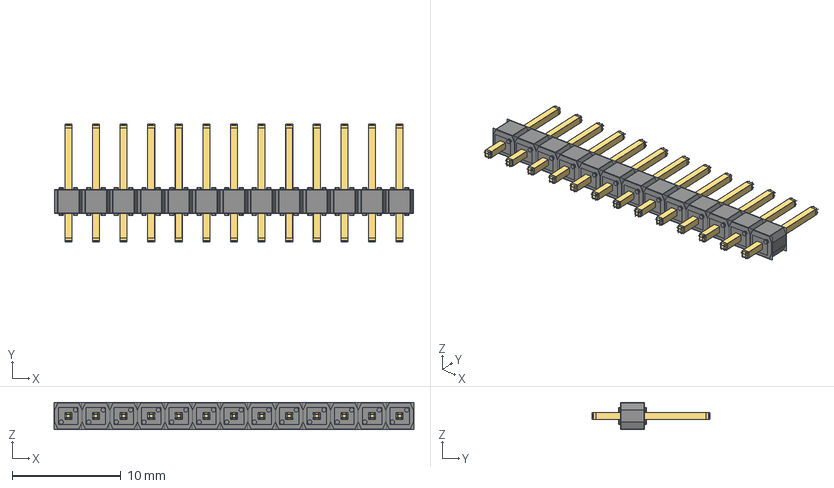
[picture p69: CAD file, 2023-05-30]
LVDC-Parts-Kicad/3dmodels/1x13.igs
33.1 x 10.8 x 2.51 mm
