discount-cactus/LVDC-Remake/LVDC-Parts-Kicad/3dmodels/BHR-60-HUA.step

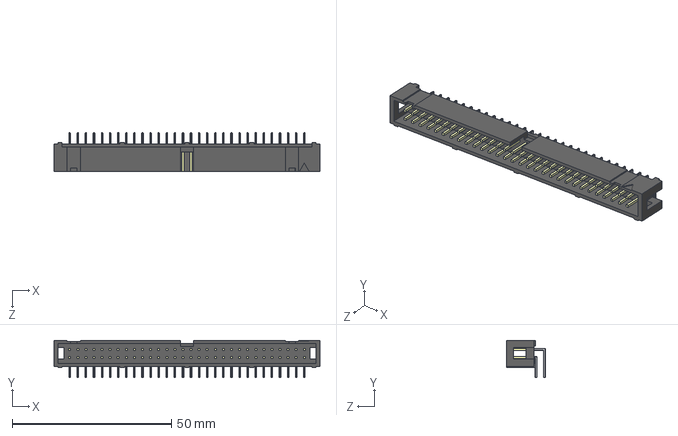
[picture p70: CAD file, 2023-05-30]
LVDC-Parts-Kicad/3dmodels/BHR-60-HUA.step
83.5 x 11.7 x 12.1 mm
