discount-cactus/LVDC-Remake/LVDC-Parts-Kicad/3dmodels/RES_PTH.step

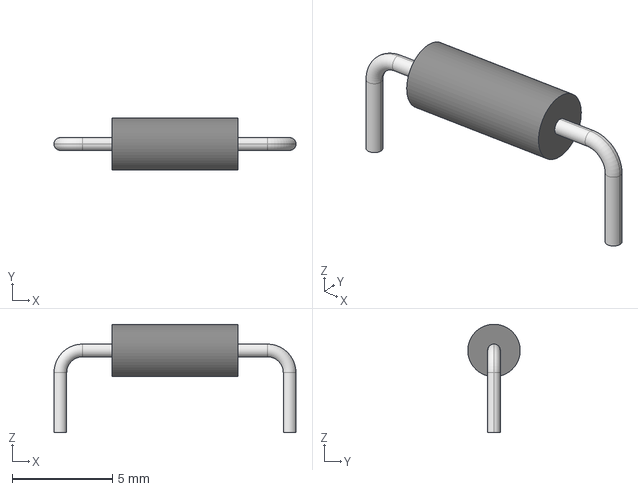
[picture p71: CAD file, 2023-05-30]
LVDC-Parts-Kicad/3dmodels/RES_PTH.step
12.1 x 2.61 x 5.41 mm
