discount-cactus/LVDC-Remake/LVDC-Parts-Kicad/3dmodels/2x14.step

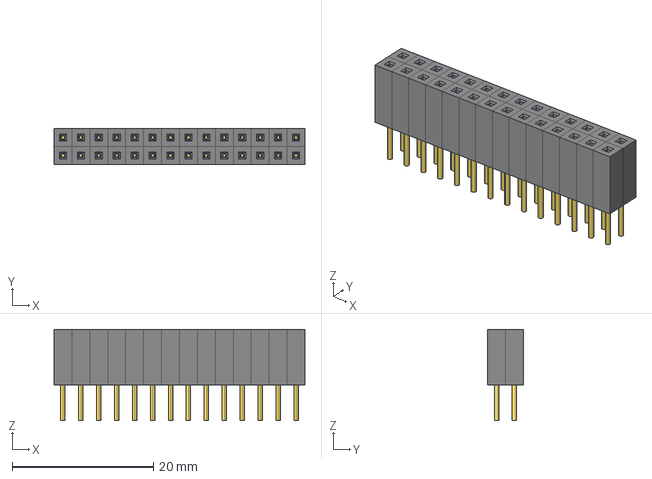
[picture p72: CAD file, 2023-05-30]
LVDC-Parts-Kicad/3dmodels/2x14.step
35.6 x 5.08 x 13.0 mm
