discount-cactus/LVDC-Remake/LVDC-Parts-Kicad/3dmodels/AT28C64B-15PU.step

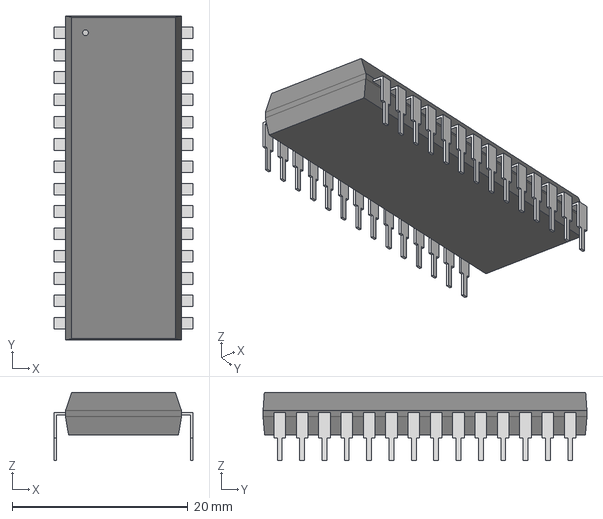
[picture p73: CAD file, 2023-05-30]
LVDC-Parts-Kicad/3dmodels/AT28C64B-15PU.step
15.7 x 36.8 x 7.75 mm
