discount-cactus/LVDC-Remake/LVDC-Parts-Kicad/3dmodels/TLP3545(F).step

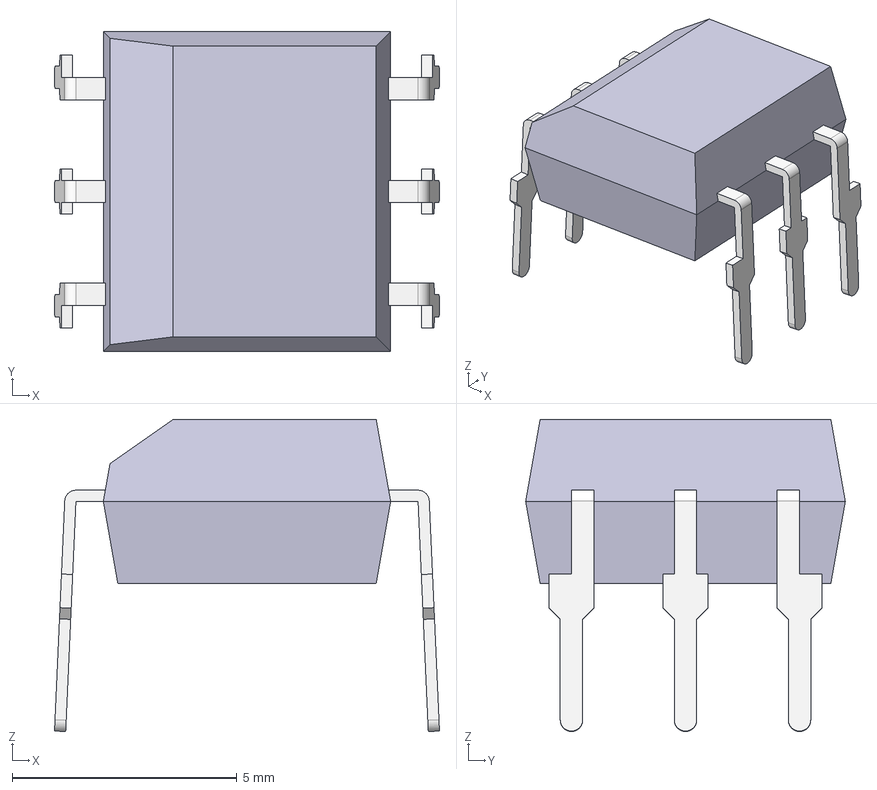
[picture p74: CAD file, 2023-05-30]
LVDC-Parts-Kicad/3dmodels/TLP3545(F).step
8.57 x 7.12 x 6.95 mm
