discount-cactus/LVDC-Remake/LVDC-Parts-Kicad/3dmodels/LM317LD13TR.step

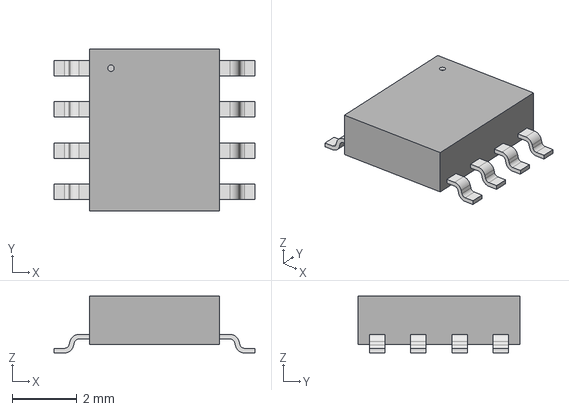
[picture p75: CAD file, 2023-05-30]
LVDC-Parts-Kicad/3dmodels/LM317LD13TR.step
6.20 x 5.00 x 1.75 mm
