discount-cactus/LVDC-Remake/LVDC-Parts-Kicad/3dmodels/MMPQ3904.step

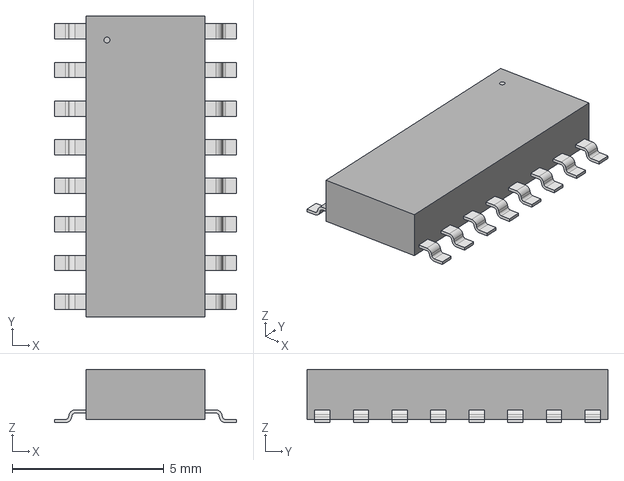
[picture p76: CAD file, 2023-05-30]
LVDC-Parts-Kicad/3dmodels/MMPQ3904.step
5.99 x 9.91 x 1.75 mm
