discount-cactus/LVDC-Remake/LVDC-Parts-Kicad/3dmodels/2x16.STEP

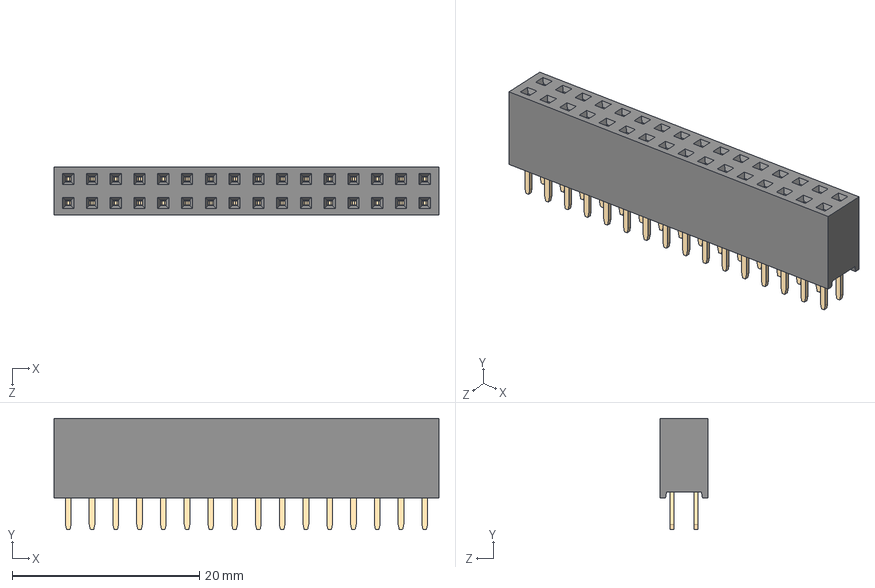
[picture p77: CAD file, 2023-05-30]
LVDC-Parts-Kicad/3dmodels/2x16.STEP
41.1 x 11.9 x 5.08 mm
2 row tin body_16
2 row tin pins x 16
