discount-cactus/LVDC-Remake/LVDC-Parts-Kicad/3dmodels/ECS-2520MV-250-CN-TR.step

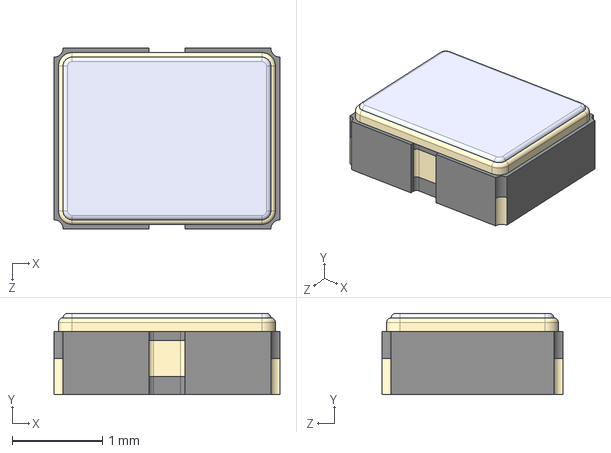
[picture p78: CAD file, 2023-05-30]
LVDC-Parts-Kicad/3dmodels/ECS-2520MV-250-CN-TR.step
2.50 x 0.9 x 2.00 mm
