discount-cactus/LVDC-Remake/LVDC-Parts-Kicad/3dmodels/CD4001BPWR.step

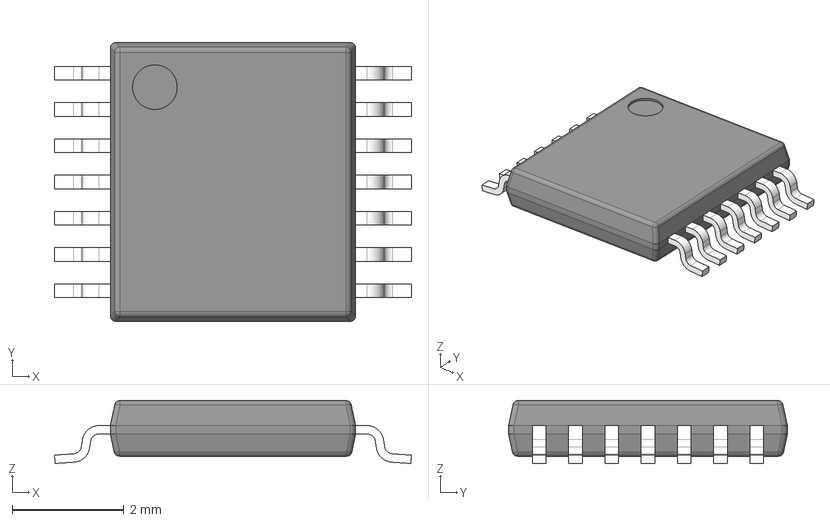
[picture p79: CAD file, 2023-04-08]
LVDC-Parts-Kicad/3dmodels/CD4001BPWR.step
6.40 x 5.00 x 1.13 mm
BODY-TSSOP
LEAD-TSSOP x 14
PIN1
