discount-cactus/LVDC-Remake/LVDC-Parts-Kicad/3dmodels/OSTTE020104.step

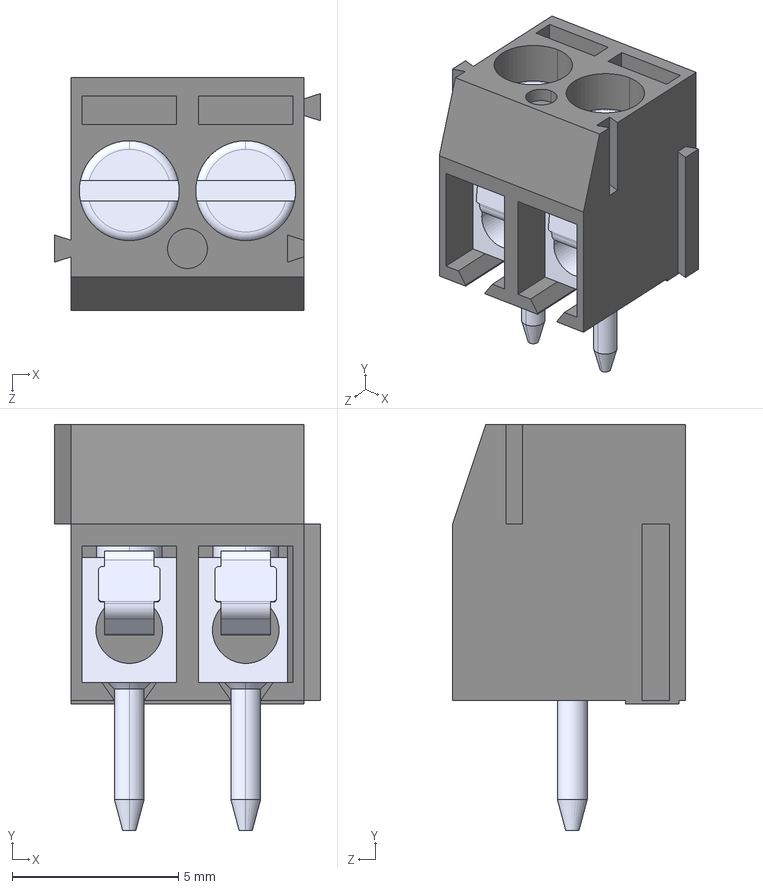
[picture p80: CAD file, 2023-04-08]
LVDC-Parts-Kicad/3dmodels/OSTTE020104.step
8.00 x 12.2 x 7.00 mm
