discount-cactus/LVDC-Remake/LVDC-Parts-Kicad/3dmodels/3557-2.step

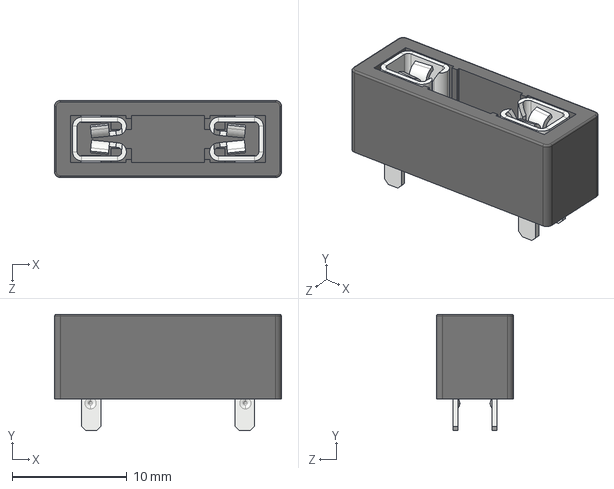
[picture p81: CAD file, 2023-04-08]
LVDC-Parts-Kicad/3dmodels/3557-2.step
19.8 x 10.2 x 6.73 mm
