discount-cactus/LVDC-Remake/LVDC-Parts-Kicad/3dmodels/NE555P.stp

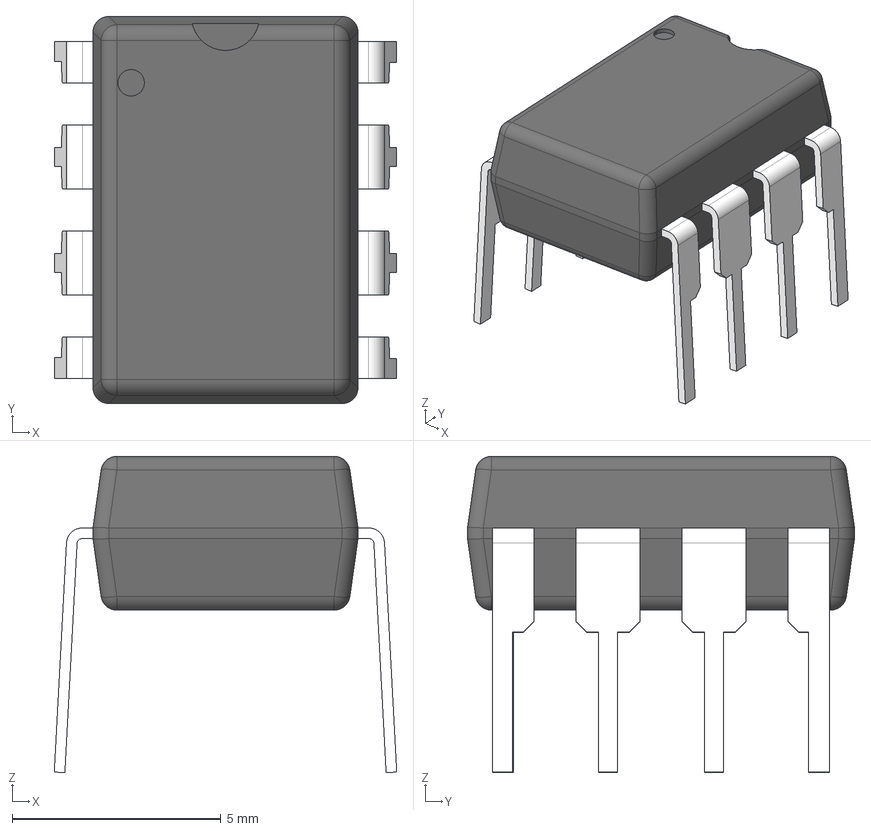
[picture p82: CAD file, 2023-04-08]
LVDC-Parts-Kicad/3dmodels/NE555P.stp
8.20 x 9.27 x 7.58 mm
BODY_P0008A
LEAD_P0008A x 4
LD_LHALF_P0008A x 2
LD_RHALF_P0008A x 2
