discount-cactus/LVDC-Remake/LVDC-Parts-Kicad/3dmodels/2x20.step

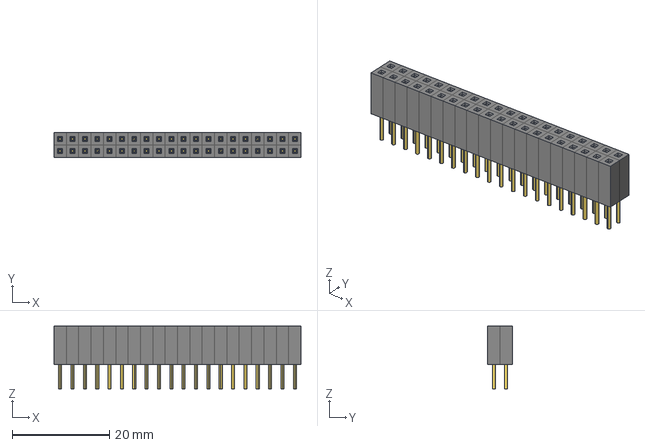
[picture p83: CAD file, 2023-04-08]
LVDC-Parts-Kicad/3dmodels/2x20.step
50.8 x 5.08 x 13.0 mm
