discount-cactus/LVDC-Remake/LVDC-Parts-Kicad/3dmodels/LED_3MM.stp

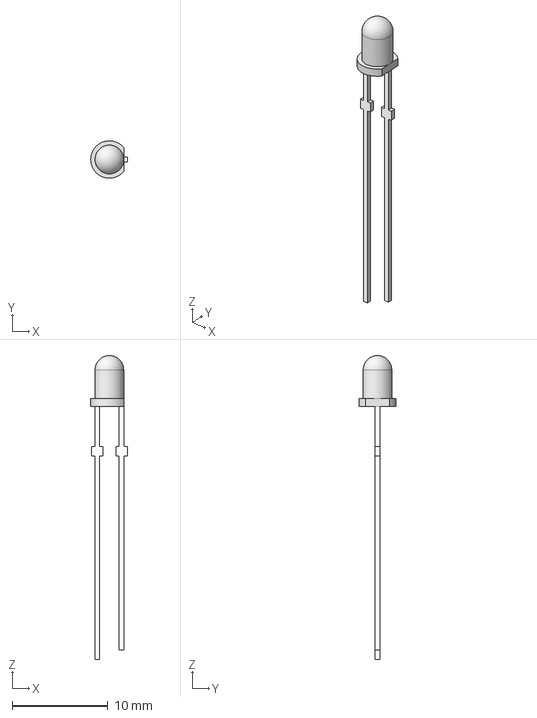
[picture p84: CAD file, 2023-04-08]
LVDC-Parts-Kicad/3dmodels/LED_3MM.stp
3.82 x 3.90 x 31.7 mm
