discount-cactus/LVDC-Remake/LVDC-Parts-Kicad/3dmodels/SOD123_DIO.step

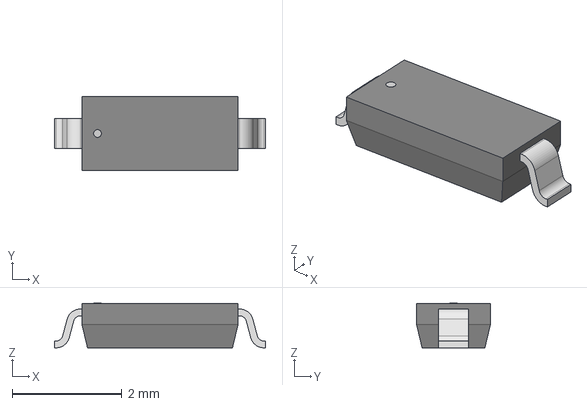
[picture p85: CAD file, 2023-04-08]
LVDC-Parts-Kicad/3dmodels/SOD123_DIO.step
3.85 x 1.35 x 0.815 mm
