discount-cactus/LVDC-Remake/LVDC-Parts-Kicad/3dmodels/C_1206.step

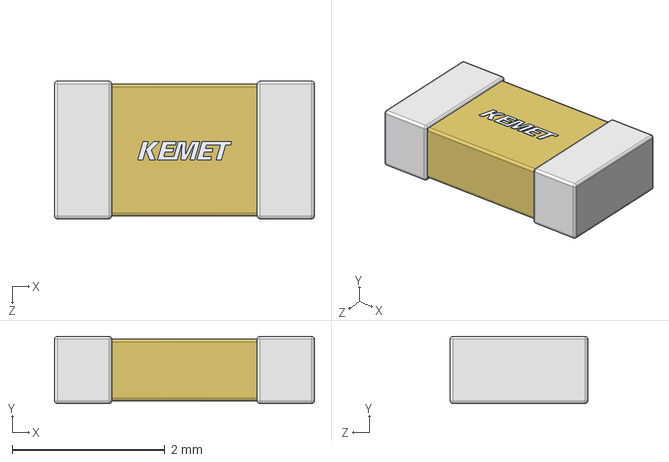
[picture p86: CAD file, 2023-04-08]
LVDC-Parts-Kicad/3dmodels/C_1206.step
3.40 x 0.88 x 1.80 mm
