discount-cactus/LVDC-Remake/LVDC-Parts-Kicad/3dmodels/NTCLE100E3102.step

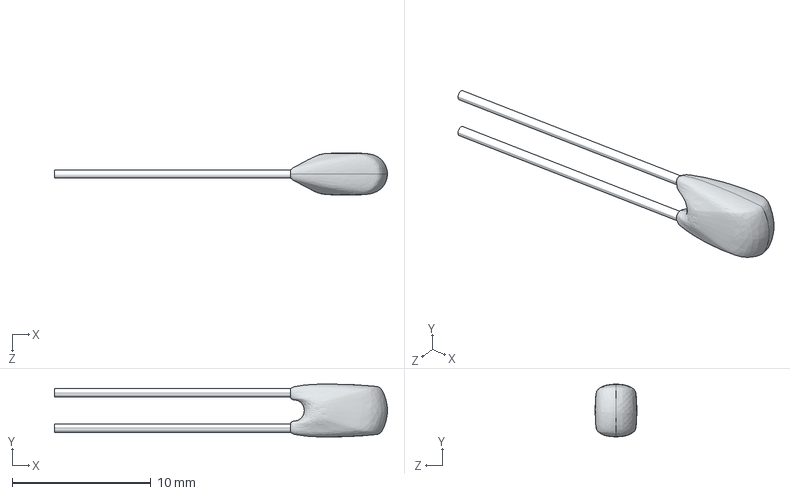
[picture p87: CAD file, 2023-04-08]
LVDC-Parts-Kicad/3dmodels/NTCLE100E3102.step
24.0 x 3.80 x 3.00 mm
