discount-cactus/LVDC-Remake/LVDC-Parts-Kicad/3dmodels/14_DIP.step

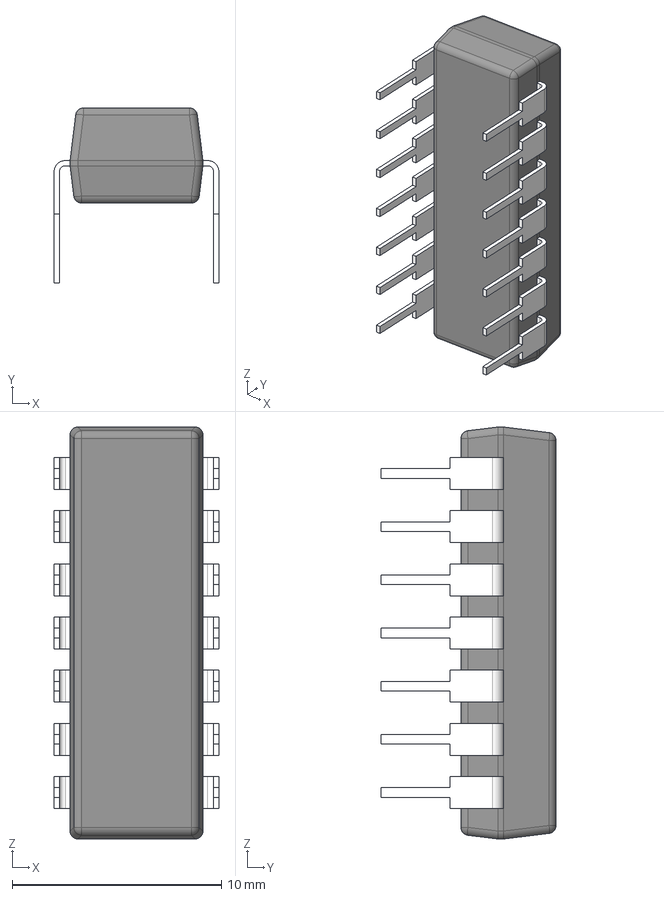
[picture p88: CAD file, 2023-04-08]
LVDC-Parts-Kicad/3dmodels/14_DIP.step
7.87 x 8.37 x 19.7 mm
BODY_N0014A_AF0
LEAD_N0014A_AF1
LEAD_N0014A x 10
LEAD_N0014A_AF3
LEAD_N0014A_AF0
LEAD_N0014A_AF2
