discount-cactus/LVDC-Remake/LVDC-Parts-Kicad/3dmodels/1x4.step

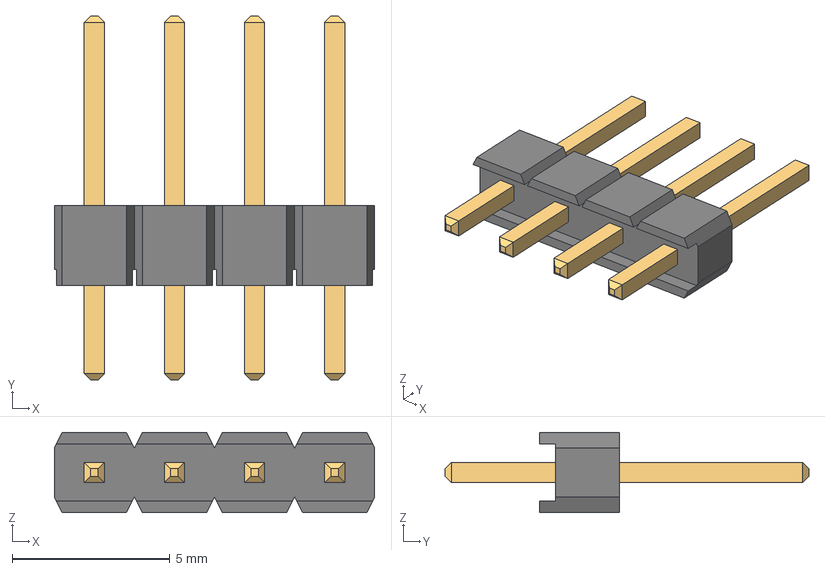
[picture p89: CAD file, 2023-04-08]
LVDC-Parts-Kicad/3dmodels/1x4.step
10.2 x 11.5 x 2.54 mm
6130xx11121_PIN x 4
