discount-cactus/LVDC-Remake/LVDC-Parts-Kicad/3dmodels/SOT23F.step

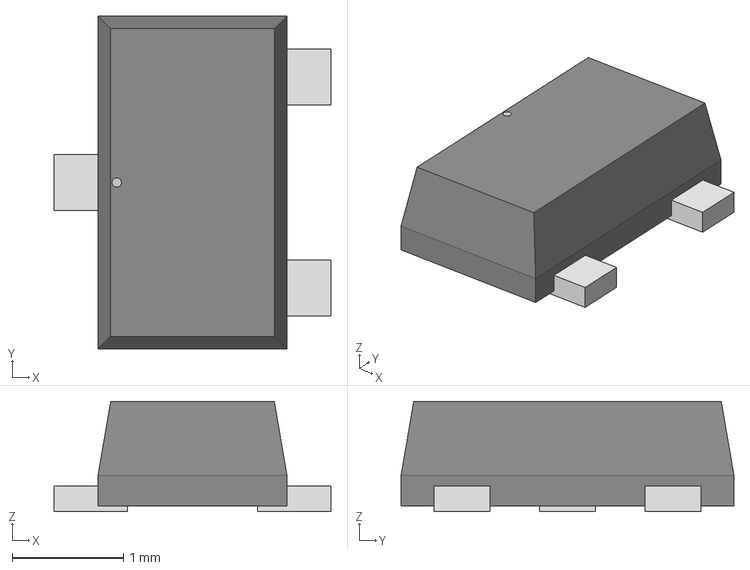
[picture p90: CAD file, 2023-04-08]
LVDC-Parts-Kicad/3dmodels/SOT23F.step
2.49 x 3.00 x 0.993 mm
