discount-cactus/LVDC-Remake/LVDC-Parts-Kicad/3dmodels/C_0603.step

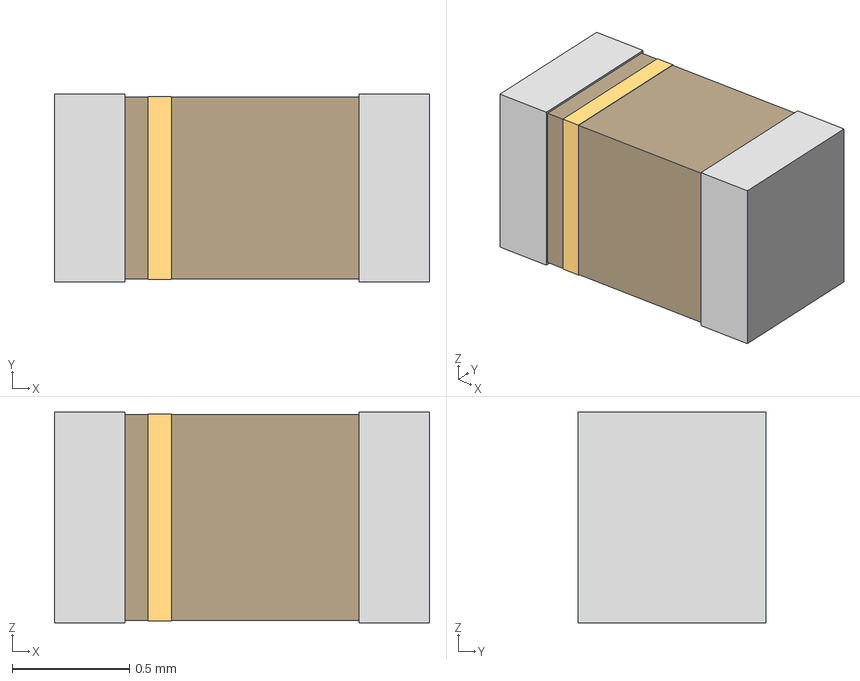
[picture p91: CAD file, 2023-04-08]
LVDC-Parts-Kicad/3dmodels/C_0603.step
1.60 x 0.8 x 0.9 mm
