discount-cactus/LVDC-Remake/LVDC-Parts-Kicad/3dmodels/1x2.step

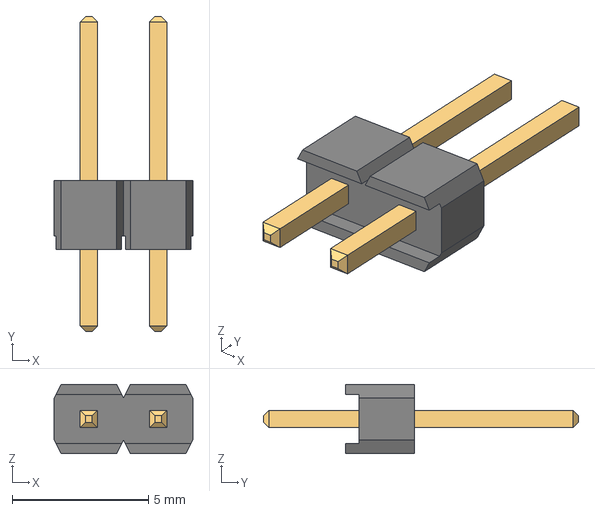
[picture p92: CAD file, 2023-04-08]
LVDC-Parts-Kicad/3dmodels/1x2.step
5.08 x 11.5 x 2.54 mm
6130xx11121_PIN x 2
