discount-cactus/LVDC-Remake/LVDC-Parts-Kicad/3dmodels/16_DIP.step

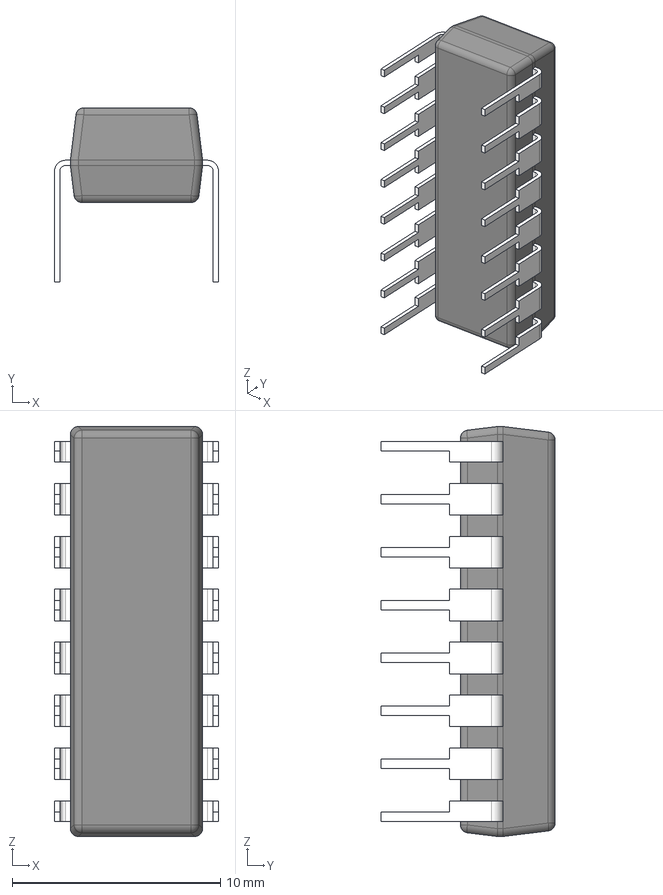
[picture p93: CAD file, 2023-04-08]
LVDC-Parts-Kicad/3dmodels/16_DIP.step
7.87 x 8.37 x 19.7 mm
BODY_N0016A_AF0
LEAD_N0016A_AF1
LEAD_N0016A x 10
LEAD_N0016A_AF3
LEAD_N0016A_AF5
LEAD_N0016A_AF0
LEAD_N0016A_AF2
LEAD_N0016A_AF4
