discount-cactus/LVDC-Remake/LVDC-Parts-Kicad/3dmodels/R_1206_stp.stp

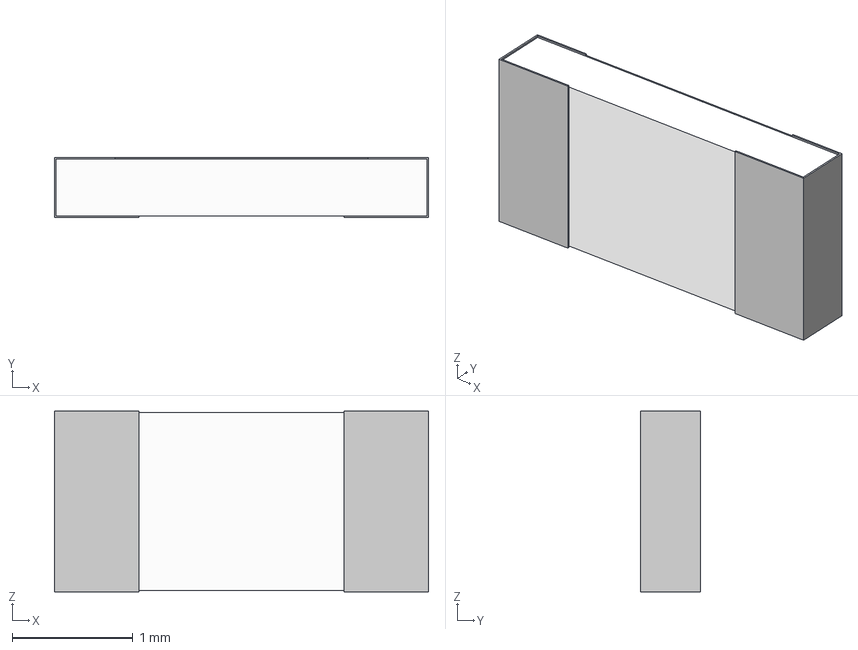
[picture p94: CAD file, 2023-04-08]
LVDC-Parts-Kicad/3dmodels/R_1206_stp.stp
3.10 x 0.5 x 1.50 mm
