discount-cactus/LVDC-Remake/LVDC-Parts-Kicad/3dmodels/R_603_stp.stp

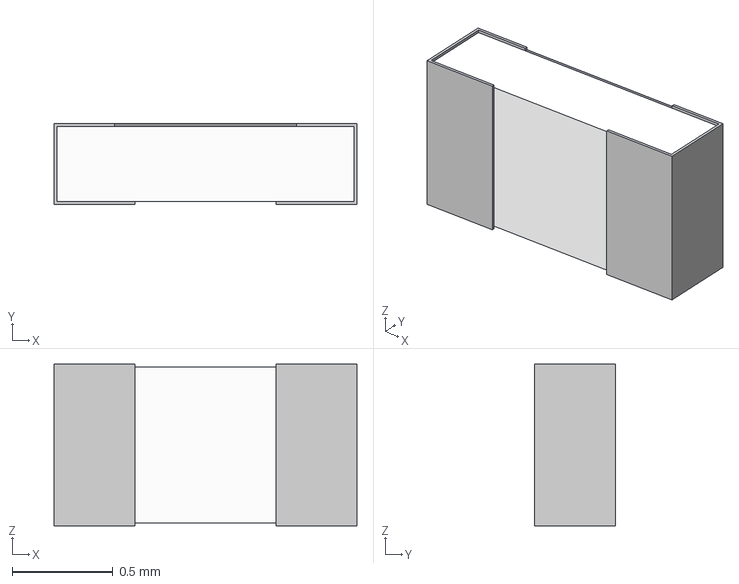
[picture p95: CAD file, 2023-04-08]
LVDC-Parts-Kicad/3dmodels/R_603_stp.stp
1.50 x 0.4 x 0.8 mm
